mewmix/asm2464-enclosure/simulation/asm2464/upstream/emulate/hardware.py

"""
ASM2464PD Hardware Emulation

This module provides realistic hardware emulation for the ASM2464PD.
Only hardware registers (XDATA >= 0x6000) are emulated here.
RAM (XDATA < 0x6000) is handled by the memory system, not this module.
"""

from typing import TYPE_CHECKING, Dict, Set, Callable, Optional
from dataclasses import dataclass, field
from enum import IntEnum
import re
import os
import hashlib
import struct

from pyrite import PyriteDevice

if TYPE_CHECKING:
    from memory import Memory


# Physical SPI NOR geometry confirmed by two independent full-device dumps.
SPI_FLASH_SIZE = 0x80000
SPI_FLASH_ERASED_BYTE = 0xFF


def validate_stock_c24c_bridge_trace(events, config, link_param=0,
                                     initial_lane_mask=0,
                                     restore_b402=False):
    """Validate the ordered controller-visible core of stock C24C/CC83.

    ``events`` contains ``(bank, address, old, new)`` tuples.  Bank zero is
    normal MMIO and bank one is the DPX switch/PHY plane.  ``config`` is the
    four-byte SPI configuration slice at offsets 0x74..0x77, ordered exactly
    as stock 8C5F-8C86 loads it: vendor high/low, device high/low.

    This intentionally stops at C7A4's B436 lane configuration.  C24C's later
    3A2B call initializes stock-private queue tables. Its controller-visible
    history has a separate strict observer; the overlapping low-XDATA tables
    are not pretended to belong to the handmade firmware. Passing this
    validator therefore proves ordered bridge reconstruction only; it does
    not prove that silicon will generate C802.2/C520.1 after a 0206 descriptor.
    """
    if len(config) != 4:
        return False
    vendor_hi, vendor_lo, device_hi, device_lo = config

    # Each entry is bank, address, and either a direct value or an RMW mask.
    # RMW entries are (and_mask, or_value).  Keeping two writes to the same
    # register as two entries is deliberate: final-state equivalence is not
    # accepted for this undocumented bridge transaction.
    expected = [
        (0, 0xB401, (0xFE, 0x01)),
        (0, 0xB401, (0xFE, 0x00)),
        (0, 0xCA06, (0xEF, 0x00)),
        (0, 0xB410, vendor_lo), (0, 0xB411, vendor_hi),
        (0, 0xB420, vendor_lo), (0, 0xB421, vendor_hi),
        (0, 0xB412, device_lo), (0, 0xB413, device_hi),
        (0, 0xB422, device_lo), (0, 0xB423, device_hi),
        (0, 0xB415, 0x06), (0, 0xB416, 0x04), (0, 0xB417, 0x00),
        (0, 0xB425, 0x06), (0, 0xB426, 0x04), (0, 0xB427, 0x00),
        (0, 0xB41A, vendor_lo), (0, 0xB41B, vendor_hi),
        (0, 0xB42A, vendor_lo), (0, 0xB42B, vendor_hi),
        (0, 0xB418, device_lo), (0, 0xB419, device_hi),
        (0, 0xB428, device_lo), (0, 0xB429, device_hi),
        (1, 0x4084, 0x22), (1, 0x5084, 0x22),
        (0, 0xB401, (0xFE, 0x01)),
        (0, 0xB482, (0xFE, 0x01)),
        (0, 0xB482, (0x0F, 0xF0)),
        (0, 0xB401, (0xFE, 0x00)),
        (0, 0xB480, (0xFE, 0x01)),
        (0, 0xB430, (0xFE, 0x00)),
        (0, 0xB298, (0xEF, 0x10)),
        (1, 0x6043, 0x70), (1, 0x6025, (0x7F, 0x80)),
        (0, 0xCA06, (0xEF, 0x00)),
        (0, 0xB480, (0xFE, 0x01)),
        (0, 0xC659, (0xFE, 0x00)),
        (0, 0xB402, (0xFD, 0x00)),
    ]
    # BEA0 retains B434's upper nibble and progressively ORs masks 1,2,4,8
    # until all requested lanes are enabled. It can therefore perform zero to
    # four writes depending on the state inherited from the link path.
    initial_lane = initial_lane_mask & 0x0F
    lane = initial_lane
    for bit in (0x01, 0x02, 0x04, 0x08):
        if lane == 0x0F:
            break
        lane |= bit
        expected.append((0, 0xB434, (0xF0, lane)))
    if restore_b402:
        expected.append((0, 0xB402, (0xFD, 0x02)))
    expected.extend((
        (0, 0xB436, (0xF0, 0x0E)),
        (0, 0xB436, (0x0F, ((~link_param) & 0x0F) << 4)),
    ))
    if len(events) != len(expected):
        return False
    register_state = {}
    for event, requirement in zip(events, expected):
        bank, address, old, new = event
        expected_bank, expected_address, operation = requirement
        if bank != expected_bank or address != expected_address:
            return False
        key = (bank, address)
        if key in register_state and old != register_state[key]:
            return False
        register_state[key] = new
        if isinstance(operation, tuple):
            and_mask, or_value = operation
            wanted = (old & and_mask) | or_value
        else:
            wanted = operation
        if new != wanted:
            return False
    b402_clear = events[39]
    if bool(b402_clear[2] & 0x02) != bool(restore_b402):
        return False
    lane_events = [event for event in events if event[0:2] == (0, 0xB434)]
    if lane_events and (lane_events[0][2] & 0x0F) != initial_lane:
        return False
    return True


def validate_stock_cc83_bridge_trace(events, config):
    """Validate stock CC83 without C24C's caller prefix or lane tail."""
    if len(config) != 4:
        return False
    vendor_hi, vendor_lo, device_hi, device_lo = config
    expected = [
        (0, 0xCA06, (0xEF, 0x00)),
        (0, 0xB410, vendor_lo), (0, 0xB411, vendor_hi),
        (0, 0xB420, vendor_lo), (0, 0xB421, vendor_hi),
        (0, 0xB412, device_lo), (0, 0xB413, device_hi),
        (0, 0xB422, device_lo), (0, 0xB423, device_hi),
        (0, 0xB415, 0x06), (0, 0xB416, 0x04), (0, 0xB417, 0x00),
        (0, 0xB425, 0x06), (0, 0xB426, 0x04), (0, 0xB427, 0x00),
        (0, 0xB41A, vendor_lo), (0, 0xB41B, vendor_hi),
        (0, 0xB42A, vendor_lo), (0, 0xB42B, vendor_hi),
        (0, 0xB418, device_lo), (0, 0xB419, device_hi),
        (0, 0xB428, device_lo), (0, 0xB429, device_hi),
        (1, 0x4084, 0x22), (1, 0x5084, 0x22),
        (0, 0xB401, (0xFE, 0x01)),
        (0, 0xB482, (0xFE, 0x01)),
        (0, 0xB482, (0x0F, 0xF0)),
        (0, 0xB401, (0xFE, 0x00)),
        (0, 0xB480, (0xFE, 0x01)),
        (0, 0xB430, (0xFE, 0x00)),
        (0, 0xB298, (0xEF, 0x10)),
        (1, 0x6043, 0x70), (1, 0x6025, (0x7F, 0x80)),
    ]
    if len(events) != len(expected):
        return False
    register_state = {}
    for event, requirement in zip(events, expected):
        bank, address, old, new = event
        expected_bank, expected_address, operation = requirement
        if (bank, address) != (expected_bank, expected_address):
            return False
        key = (bank, address)
        if key in register_state and old != register_state[key]:
            return False
        register_state[key] = new
        wanted = ((old & operation[0]) | operation[1]
                  if isinstance(operation, tuple) else operation)
        if new != wanted:
            return False
    return True

# =============================================================================
# Register Name Lookup
# =============================================================================
# Parse registers.h to build addr -> name lookup table

_REGISTER_NAMES: Dict[int, str] = {}

def _load_register_names():
    """Parse registers.h and build address-to-name lookup table."""
    global _REGISTER_NAMES
    if _REGISTER_NAMES:
        return  # Already loaded

    # Find registers.h relative to this file
    this_dir = os.path.dirname(os.path.abspath(__file__))
    registers_h = os.path.join(this_dir, '..', 'src', 'include', 'registers.h')

    if not os.path.exists(registers_h):
        return

    # Pattern: #define REG_NAME  XDATA_REG8(0xADDR) or similar
    pattern = re.compile(r'#define\s+(REG_\w+)\s+XDATA_REG\d+\((0x[0-9A-Fa-f]+)\)')

    with open(registers_h, 'r') as f:
        for line in f:
            match = pattern.search(line)
            if match:
                name = match.group(1)
                addr = int(match.group(2), 16)
                _REGISTER_NAMES[addr] = name

def get_register_name(addr: int) -> str:
    """Get register name for address, or empty string if unknown."""
    _load_register_names()
    return _REGISTER_NAMES.get(addr, "")


class USBState(IntEnum):
    """
    USB state machine states.

    Matches firmware I_USB_STATE (IDATA[0x6A]) and USB_STATE_* constants in globals.h.
    State transitions occur in ISR at 0x0E68 and main loop at 0x202A.
    """
    DISCONNECTED = 0  # USB_STATE_DISCONNECTED - No USB connection
    ATTACHED = 1      # USB_STATE_ATTACHED - Cable connected
    POWERED = 2       # USB_STATE_POWERED - Bus powered
    DEFAULT = 3       # USB_STATE_DEFAULT - Default address assigned
    ADDRESS = 4       # USB_STATE_ADDRESS - Device address assigned
    CONFIGURED = 5    # USB_STATE_CONFIGURED - Ready for vendor commands


@dataclass
class USBCommand:
    """USB command queued for firmware processing."""
    cmd: int           # Command type (0xE4=read, 0xE5=write, 0x8A=scsi)
    addr: int          # Target XDATA address
    data: bytes        # Data for write commands
    response: bytes = b''  # Response data for read commands


class USBController:
    """
    USB controller emulation using only MMIO registers.

    This class manages the USB state machine and vendor command injection
    without directly modifying RAM. All state transitions are driven by
    setting MMIO registers that cause the firmware to naturally progress
    through its USB state machine.

    The firmware's USB state machine:
    - I_USB_STATE (IDATA[0x6A]) contains current USB state (0-5)
    - State 5 = USB_STATE_CONFIGURED, ready for vendor commands
    - Firmware transitions states by reading MMIO and updating its own RAM

    Key MMIO registers for USB (see registers.h for full definitions):
    - REG_USB_STATUS (0x9000): Connection status (bit 7=connected, bit 0=active)
    - REG_USB_PERIPH_STATUS (0x9101): Interrupt flags (bit 5 triggers cmd handler)
    - REG_USB_CTRL_PHASE (0x9091): Control transfer phase (bit 0=setup, bit 1=data)
    - REG_USB_DMA_TRIGGER (0x9092): Trigger DMA for descriptor transfer
    - REG_USB_DMA_STATE (0xCE89): DMA state machine (bits control transitions)
    - REG_USB_SETUP_* (0x9E00-0x9E07): USB setup packet buffer
    - REG_USB_EP0_COMPLETE (0xE712): EP0 transfer complete status

    Key globals for USB (see globals.h):
    - G_CMD_SLOT_INDEX (0x05A3): Current command slot index
    - G_CMD_TABLE_BASE (0x05B1): Command table (10 x 34-byte entries)
    - G_USB_CMD_CONFIG (0x07EC): USB command configuration
    - G_DMA_XFER_STATUS (0x0AA0): DMA transfer status
    """

    def __init__(self, hw: 'HardwareState'):
        self.hw = hw
        self.state = USBState.DISCONNECTED
        self.pending_cmd: Optional[USBCommand] = None
        self.enumeration_complete = False
        self.vendor_cmd_active = False

        # Track state machine progress
        self.state_machine_reads = 0
        self.enumeration_step = 0

        # Pending descriptor request from GET_DESCRIPTOR
        self.pending_descriptor_request = None

    def connect(self, speed: int = 2):
        """
        Simulate USB cable connection via MMIO registers.

        This sets the initial MMIO state that triggers USB enumeration
        in the firmware. The firmware will progress through states 0→5.

        Args:
            speed: USB speed mode:
                0 = Full Speed (USB 1.x, 12 Mbps)
                1 = High Speed (USB 2.0, 480 Mbps)
                2 = SuperSpeed (USB 3.x, 5 Gbps)
                3 = SuperSpeed+ (USB 3.1+, 10+ Gbps)
        """
        self.state = USBState.ATTACHED
        self.enumeration_step = 1
        self.usb_speed = speed

        # USB connection status registers
        # NOTE: 0x9000 bit 0 must be SET to enter USB state machine at 0x0E6E
        # At ISR 0x0E68: if bit 0 SET, jump to USB handling at 0x0E6E
        self.hw.regs[0x9000] = 0x81  # Bit 7 (connected), bit 0 SET for USB handling
        self.hw.regs[0x90E0] = speed  # USB speed
        self.hw.regs[0x9100] = speed  # USB link active with speed
        self.hw.regs[0x9105] = 0xFF  # PHY active
        # USB state indicator (0x9118):
        # At ISR 0x0E71, value is used as index into table at 0x5AC9
        # If table[0x9118] >= 8, USB handling is skipped
        # table[0] = 0x08 (skip), table[1] = 0x00 (continue)
        # Set to 1 to enable USB enumeration handling
        self.hw.regs[0x9118] = 0x01  # USB enumeration state (1 = pending setup)

        # USB interrupt and state machine triggers:
        # At 0x0FEB: if 0x9101 bit 6 CLEAR, skip USB init path
        # At 0x0FF2: if 0x90E2 bit 0 CLEAR, skip USB init path
        # So both bit 6 of 0x9101 and bit 0 of 0x90E2 must be SET
        self.hw.regs[0xC802] = 0x05  # USB interrupt pending (bits 0 + 2)
        self.hw.regs[0x9101] = 0x61  # Bit 6 SET (USB init), bit 5 SET, bit 0 for USB active
        self.hw.regs[0x90E2] = 0x03  # Bit 0 SET (USB init trigger), bit 1 SET

        # USB restart trigger at 0xCC5D:
        # At 0x2163-0x216B: if bit 0 CLEAR and bit 1 SET, calls USB restart at 0x2176
        # This sets 0x0A5A=1 which enables the USB init path at 0x2185
        self.hw.regs[0xCC5D] = 0x02  # Bit 1 SET, bit 0 CLEAR - triggers USB restart

        # USB PHY control at 0x91C0:
        # Firmware clears this during init, but at 0x203B it checks bit 1.
        # When state 0x0A59 == 2, if 0x92C2 bit 6 is SET and 0x91C0 bit 1 is SET,
        # firmware calls 0x0322 which progresses the USB state machine.
        self.hw.regs[0x91C0] = 0x02  # Bit 1 SET - enables USB state machine progress

        # USB mode indicators for descriptor handling at 0xA7E5 and 0x87A1:
        # At 0xA7E4-0xA7E5: checks 0xCC91 bit 1 for USB3 mode
        # At 0xA7FD-0xA7FF: checks 0x09F9 bit 6 for USB3 speed
        # If both set, 0x0ACC gets value with bit 1 SET, enabling USB3 descriptor path
        # For USB 2.0: clear these bits so firmware takes USB2 path
        if speed >= 2:  # SuperSpeed or higher
            self.hw.regs[0xCC91] = 0x02  # Bit 1 SET - USB3 mode
            self.hw.regs[0x09F9] = 0x40  # Bit 6 SET - USB3 speed indicator
        else:  # High Speed or Full Speed (USB 2.0)
            self.hw.regs[0xCC91] = 0x00  # Bit 1 CLEAR - USB2 mode
            self.hw.regs[0x09F9] = 0x00  # Bit 6 CLEAR - USB2 speed indicator

        # PCIe enumeration state - simulate that PCIe link is already up
        # In real hardware, PCIe enumeration happens during boot before USB control
        # transfers. The firmware checks this state at 0x185C before taking the
        # descriptor DMA path (0x1865+). Without it, firmware takes alternate path.
        #
        # Flow: 0x3803 checks XDATA[0x053F] or XDATA[0x0553] != 0
        #       If true, sets XDATA[0x0AF7] = 1 at 0x3914-0x3919
        #       This enables the "good" path at 0x185C that uses descriptor DMA
        #
        # CRITICAL: 0xB480 bit 0 must be SET to prevent firmware at 0x20DA from
        # taking the path at 0x20F9 that clears XDATA[0x0AF7] to 0.
        # At 0x20DA: jnb acc.0, 0x20fe -> if bit 0 CLEAR, jump and clear 0x0AF7
        self.hw.regs[0xB480] = 0x03  # Bits 0,1 SET - PCIe link active state

        # Set these to simulate completed PCIe enumeration:
        if self.hw.memory:
            self.hw.memory.xdata[0x0AF7] = 0x01  # PCIe enumeration complete flag
            self.hw.memory.xdata[0x053F] = 0x01  # PCIe link state (port 0)
            # CRITICAL: Command table state at G_CMD_TABLE_BASE + index*0x22 must NOT be 4
            # At 0x35D4-0x35DF: Firmware calls 0x1551 which reads G_CMD_SLOT_INDEX (0x05A3),
            # then calculates G_CMD_TABLE_BASE[index] and if that value equals 4,
            # it calls 0x54BB which clears XDATA[0x0AF7] to 0.
            # Set slot 0 state to 3 (ready) instead of 4 (error/reset).
            self.hw.memory.xdata[0x05A3] = 0x00  # G_CMD_SLOT_INDEX = 0
            self.hw.memory.xdata[0x05B1] = 0x03  # G_CMD_TABLE_BASE[0] = 3 (ready)

        print(f"[{self.hw.cycles:8d}] [USB_CTRL] Connected - MMIO set for enumeration")

    def inject_bot_cbw(self, cdb: bytes, *, tag: int = 1, transfer_length: int = 0,
                       direction_in: bool = False, lun: int = 0,
                       signature: bytes = b'USBC', cbw_length: int = 31,
                       flags: Optional[int] = None,
                       cdb_length: Optional[int] = None):
        """Inject a BOT CBW using the controller's parsed 0x911B layout."""
        if not self.hw.usb_bulk_engine_active:
            raise RuntimeError("BOT endpoint engine is not active")
        if not self.hw.usb_cbw_armed:
            raise RuntimeError("BOT CBW parser is not armed")
        if len(signature) != 4:
            raise ValueError("BOT signature must contain exactly four bytes")
        if not 1 <= len(cdb) <= 16:
            raise ValueError("BOT CDB length must be between 1 and 16 bytes")
        if not 0 <= transfer_length <= 0xFFFFFFFF:
            raise ValueError("BOT transfer length is outside uint32 range")

        regs = self.hw.regs
        regs[0x9119] = (cbw_length >> 8) & 0xFF
        regs[0x911A] = cbw_length & 0xFF
        for i, value in enumerate(signature):
            regs[0x911B + i] = value
        for i in range(4):
            regs[0x911F + i] = (tag >> (8 * i)) & 0xFF
            regs[0x9123 + i] = (transfer_length >> (8 * i)) & 0xFF
        regs[0x9127] = flags if flags is not None else (0x80 if direction_in else 0x00)
        regs[0x9128] = lun & 0xFF
        regs[0x9129] = len(cdb) if cdb_length is None else cdb_length
        for i in range(16):
            regs[0x912A + i] = cdb[i] if i < len(cdb) else 0

        self.hw.usb_stock_cbw_dma_trace = []
        self.hw.usb_stock_cbw_dma_ready = False
        self.hw.usb_stock_cbw_tag_trace = []
        self.hw.usb_stock_cbw_tag_ready = False
        self.hw.usb_stock_bulk_in_arm_trace = []
        self.hw.usb_stock_bulk_in_arm_ready = False
        self.hw.usb_stock_bulk_in_event_ready = False
        self.hw.usb_stock_bot_alt0_service_trace = []
        self.hw.usb_cbw_armed = False
        regs[0xC802] = 0x01
        regs[0x9101] = 0x40
        self.hw._pending_usb_interrupt = True

    def complete_msc_in(self, endpoint: int = 0x81):
        """Signal completion of the last firmware-originated MSC IN transfer."""
        self.hw.regs[0x9118] = endpoint
        # Stock's BOT-alt-zero 0EF4 route requires 9096.0 in addition to
        # C802.0/9101.5. This is a modeled host-completion event, not endpoint
        # state synthesized from descriptors.
        self.hw.regs[0x9096] = self.hw.regs.get(0x9096, 0) | 0x01
        self.hw.usb_ep_ready_ack_pending = True
        self.hw.regs[0xC802] = 0x01
        self.hw.regs[0x9101] = 0x20
        self.hw._pending_usb_interrupt = True

    def inject_bot_data_out(self, data: bytes, *, buffer_offset: int = 0):
        """Deliver one BOT OUT completion into the hardware's XDATA buffer.

        This is one controller completion, not necessarily one complete BOT data
        phase.  Physical SuperSpeed hardware completed a 4096-byte host write
        after its first 1024-byte packet.  Tests that pass 4096 bytes here are
        deliberately exercising idealized state-machine logic, not the observed
        endpoint packetization.
        """
        if len(data) > 0x1000:
            raise ValueError("BOT data-out exceeds the 4 KiB hardware buffer")
        if not 0 <= buffer_offset <= 0x1000 - len(data):
            raise ValueError("BOT data-out buffer range exceeds the 4 KiB hardware buffer")
        if not self.hw.memory:
            raise RuntimeError("BOT data-out requires attached XDATA memory")
        if self.hw.usb_sw_dma_out_destination is not None:
            start = self.hw.usb_sw_dma_out_destination
            self.hw.usb_sw_dma_out_destination = None
            if buffer_offset:
                raise ValueError(
                    "buffer_offset cannot override firmware-selected SW DMA")
        else:
            start = 0x7000 + buffer_offset
        if start + len(data) > len(self.hw.memory.xdata):
            raise ValueError("BOT data-out DMA range exceeds XDATA")
        self.hw.memory.xdata[start:start + len(data)] = data
        self.hw.regs[0x910D] = (len(data) >> 8) & 0xFF
        self.hw.regs[0x910E] = len(data) & 0xFF
        self.hw.regs[0x9093] = 0x02
        self.hw.regs[0xC802] = 0x01
        self.hw.regs[0x9101] = 0x04
        self.hw._pending_usb_interrupt = True

    def advance_enumeration(self):
        """
        Advance USB enumeration state via MMIO.

        Called when firmware polls 0xCE89 to check enumeration progress.
        Each call advances the emulated enumeration sequence.
        """
        self.state_machine_reads += 1

        # Return value for 0xCE89 based on enumeration progress
        value = 0x00

        if self.state_machine_reads >= 3:
            value |= 0x01  # Bit 0 - exit wait loop at 0x348C
            self.enumeration_step = max(self.enumeration_step, 2)

        if self.state_machine_reads >= 5:
            value |= 0x02  # Bit 1 - successful enumeration path at 0x3493
            self.enumeration_step = max(self.enumeration_step, 3)

        if self.state_machine_reads >= 7:
            value |= 0x04  # Bit 2 - state 3→4→5 transitions
            self.enumeration_step = max(self.enumeration_step, 4)
            self.enumeration_complete = True
            self.state = USBState.CONFIGURED

        return value

    def inject_vendor_command(self, cmd_type: int, xdata_addr: int,
                               value: int = 0, size: int = 1):
        """
        Inject a USB vendor command via MMIO registers.

        This sets up the MMIO registers needed for the firmware to process
        a vendor command. The firmware reads these registers and handles
        the command through its normal code path.

        No direct RAM writes are performed - the firmware reads expected
        values through MMIO hooks that simulate hardware behavior.

        Args:
            cmd_type: 0xE4 (read) or 0xE5 (write)
            xdata_addr: Target XDATA address
            value: Value for write commands
            size: Size for read commands
        """
        # Build USB address format: (addr & 0x1FFFF) | 0x500000
        usb_addr = (xdata_addr & 0x1FFFF) | 0x500000

        # Build 6-byte CDB (Command Descriptor Block)
        cdb = bytes([
            cmd_type,
            size if cmd_type == 0xE4 else value,
            (usb_addr >> 16) & 0xFF,
            (usb_addr >> 8) & 0xFF,
            usb_addr & 0xFF,
            0x00
        ])

        print(f"[{self.hw.cycles:8d}] [USB_CTRL] === INJECT VENDOR COMMAND ===")
        print(f"[{self.hw.cycles:8d}] [USB_CTRL] cmd=0x{cmd_type:02X} addr=0x{xdata_addr:04X} "
              f"{'size' if cmd_type == 0xE4 else 'val'}=0x{cdb[1]:02X}")
        print(f"[{self.hw.cycles:8d}] [USB_CTRL] CDB: {cdb.hex()}")

        # =====================================================
        # MMIO REGISTER SETUP FOR VENDOR COMMAND
        # =====================================================

        # Write CDB to USB interface registers (0x910D-0x9112)
        # Firmware reads these at 0x31C0+ to get command data
        for i, b in enumerate(cdb):
            self.hw.regs[0x910D + i] = b

        # Also populate 0x911F-0x9122 (another CDB location read by 0x3186)
        for i, b in enumerate(cdb[:4]):
            self.hw.regs[0x911F + i] = b

        # USB endpoint buffers
        for i, b in enumerate(cdb):
            self.hw.usb_ep_data_buf[i] = b
            self.hw.usb_ep0_buf[i] = b
        self.hw.usb_ep0_len = len(cdb)

        # USB connection and interrupt status
        # NOTE: 0x9000 bit 0 must be CLEAR to reach the 0x5333 vendor handler path
        # At 0x0E68, JB 0xe0.0 jumps away if bit 0 is set
        self.hw.regs[0x9000] = 0x80  # Connected (bit 7), bit 0 CLEAR for vendor path
        self.hw.regs[0x9101] = 0x21  # Bit 5 triggers command handler path
        self.hw.regs[0xC802] = 0x05  # USB interrupt pending

        # USB endpoint status - signals data available
        self.hw.regs[0x9096] = 0x01  # EP0 has data
        self.hw.regs[0x90E2] = 0x01  # Endpoint status bit

        # USB command interface registers
        self.hw.regs[0xE4E0] = cdb[0]  # Command type (0xE4/0xE5)
        self.hw.regs[0xE091] = size    # Read size / write value

        # Original firmware E5 path reads these (0x17FD-0x188B)
        # 0xC47A: Value byte copied to IDATA[0x38] at 0x1801
        # 0xCEB0: Command type copied to IDATA[0x39] at 0x188B
        self.hw.regs[0xC47A] = value if cmd_type == 0xE5 else size
        self.hw.regs[0xCEB0] = 0x05 if cmd_type == 0xE5 else 0x04

        # Target address registers (read at 0x323A-0x3249)
        # CEB2 = high byte of XDATA address
        # CEB3 = low byte of XDATA address
        self.hw.regs[0xCEB2] = (xdata_addr >> 8) & 0xFF
        self.hw.regs[0xCEB3] = xdata_addr & 0xFF

        # Store E5 value separately so it survives firmware clearing 0xC47A
        if cmd_type == 0xE5:
            self.hw.usb_e5_pending_value = value

        # USB EP0 data registers (read by various helpers)
        self.hw.regs[0x9E00] = cdb[0]  # bmRequestType / cmd type
        self.hw.regs[0x9E01] = cdb[1]  # bRequest / size
        self.hw.regs[0x9E02] = cdb[4]  # wValue low / addr low
        self.hw.regs[0x9E03] = cdb[3]  # wValue high / addr mid
        self.hw.regs[0x9E04] = cdb[2]  # wIndex low / addr high
        self.hw.regs[0x9E05] = 0x00    # wIndex high
        self.hw.regs[0x9E06] = size    # wLength low
        self.hw.regs[0x9E07] = 0x00    # wLength high

        # PCIe/DMA status for command processing
        self.hw.regs[0xC47B] = 0x01  # Non-zero for checks
        self.hw.regs[0xC471] = 0x01  # Queue busy
        self.hw.regs[0xB432] = 0x07  # PCIe link status
        self.hw.regs[0xE765] = 0x02  # Ready flag

        # Store command state
        self.hw.usb_cmd_type = cmd_type
        self.hw.usb_cmd_size = size if cmd_type == 0xE4 else 0
        self.hw.usb_cmd_pending = True
        self.vendor_cmd_active = True

        # Reset E5 DMA tracking flag for new command
        self.hw._e5_dma_done = False

        # Reset state machine for fresh command processing
        self.hw.usb_ce89_read_count = 0

        print(f"[{self.hw.cycles:8d}] [USB_CTRL] MMIO registers configured")

        # =====================================================
        # USB Hardware DMA - populate RAM like real hardware
        # =====================================================
        # The USB controller populates these RAM locations via DMA
        # before triggering the interrupt. This is how real hardware works.
        if self.hw.memory:
            # USB state = 5 (configured) - set by USB enumeration
            self.hw.memory.idata[0x6A] = 5

            # USB config check at 0x35C0 - must be 0 for vendor path
            self.hw.memory.xdata[0x07EC] = 0x00

            # CDB area - USB hardware writes CDB to XDATA[0x0002+]
            # The SCSI handler at 0x32E4 reads CDB from this area
            for i, b in enumerate(cdb):
                self.hw.memory.xdata[0x0002 + i] = b

            # Vendor command flag at 0x4583 - bit 3 enables vendor dispatch
            # This overlaps with CDB area but has special meaning
            self.hw.memory.xdata[0x0003] = 0x08

            # Command type marker for table lookup at 0x35D8
            if cmd_type == 0xE4:
                self.hw.memory.xdata[0x05B1] = 0x04
            elif cmd_type == 0xE5:
                self.hw.memory.xdata[0x05B1] = 0x05

            # Command index = 0 for table lookup at 0x1551
            # 0x17B1 copies 0x05A5 to 0x05A3, so set both to 0
            self.hw.memory.xdata[0x05A3] = 0x00
            self.hw.memory.xdata[0x05A5] = 0x00

        return cdb

    def inject_scsi_write_command(self, lba: int, sectors: int, data: bytes):
        """
        Inject a 0x8A SCSI write command via MMIO registers.

        This sets up the MMIO registers and RAM needed for the firmware to process
        a SCSI write command. The firmware reads these registers and handles
        the command through its normal code path.

        Args:
            lba: Logical Block Address to write to
            sectors: Number of sectors to write (each sector is 512 bytes)
            data: Data to write (will be padded to sector boundary)
        """
        import struct

        # Build 16-byte CDB for SCSI write command
        # Format: struct.pack('>BBQIBB', 0x8A, 0, lba, sectors, 0, 0)
        cdb = struct.pack('>BBQIBB', 0x8A, 0x00, lba, sectors, 0x00, 0x00)

        print(f"[{self.hw.cycles:8d}] [USB_CTRL] === INJECT SCSI WRITE COMMAND ===")
        print(f"[{self.hw.cycles:8d}] [USB_CTRL] LBA={lba} sectors={sectors} data_len={len(data)}")
        print(f"[{self.hw.cycles:8d}] [USB_CTRL] CDB: {cdb.hex()}")

        # =====================================================
        # MMIO REGISTER SETUP FOR SCSI COMMAND
        # =====================================================

        # Write CDB to USB interface registers (0x910D-0x911C)
        for i, b in enumerate(cdb):
            self.hw.regs[0x910D + i] = b

        # USB endpoint buffers - write CDB
        for i, b in enumerate(cdb):
            self.hw.usb_ep_data_buf[i] = b
            self.hw.usb_ep0_buf[i] = b
        self.hw.usb_ep0_len = len(cdb)

        # USB connection and interrupt status
        self.hw.regs[0x9000] = 0x80  # Connected (bit 7), bit 0 CLEAR
        self.hw.regs[0x9101] = 0x21  # Bit 5 triggers command handler path
        self.hw.regs[0xC802] = 0x05  # USB interrupt pending

        # USB endpoint status
        self.hw.regs[0x9096] = 0x01  # EP0 has data
        self.hw.regs[0x90E2] = 0x01  # Endpoint status bit

        # Store command state
        self.hw.usb_cmd_type = 0x8A
        self.hw.usb_cmd_size = sectors * 512
        self.hw.usb_cmd_pending = True
        self.vendor_cmd_active = True

        # Reset state machine
        self.hw.usb_ce89_read_count = 0

        print(f"[{self.hw.cycles:8d}] [USB_CTRL] MMIO registers configured for SCSI write")

        # =====================================================
        # RAM SETUP - populate RAM like USB hardware DMA
        # =====================================================
        if self.hw.memory:
            # USB state = 5 (configured)
            self.hw.memory.idata[0x6A] = 5

            # CDB area - USB hardware writes CDB to XDATA
            for i, b in enumerate(cdb):
                self.hw.memory.xdata[0x0002 + i] = b

            # SCSI command flag
            self.hw.memory.xdata[0x0003] = 0x08

            # Command type marker - 0x8A maps to different handler
            self.hw.memory.xdata[0x05B1] = 0x8A

            # Pad data to sector boundary and write to USB data buffer at 0x8000
            padded_size = sectors * 512
            padded_data = data + b'\x00' * (padded_size - len(data))
            for i, b in enumerate(padded_data):
                if 0x8000 + i < 0x10000:  # Stay within XDATA bounds
                    self.hw.memory.xdata[0x8000 + i] = b

            # Store data length info
            self.hw.usb_data_len = len(padded_data)

            print(f"[{self.hw.cycles:8d}] [USB_CTRL] Wrote {len(padded_data)} bytes to USB buffer at 0x8000")

        return cdb

    def inject_scsi_vendor_command(self, opcode: int, cdb: bytes, data: bytes = b'',
                                    is_write: bool = False):
        """
        Inject a SCSI vendor command (E0-E8) via MMIO registers.

        This sets up the MMIO registers needed for the firmware to process
        vendor-specific SCSI commands used by patch.py for firmware updates.

        Vendor opcodes:
            0xE0 - Config Read (128 bytes)
            0xE1 - Config Write (128 bytes)
            0xE2 - Flash Read
            0xE3 - Firmware Write (to SPI flash)
            0xE4 - XDATA Read
            0xE5 - XDATA Write
            0xE6 - NVMe Admin passthrough
            0xE8 - Reset/Commit

        Args:
            opcode: SCSI vendor opcode (0xE0-0xE8)
            cdb: Complete CDB bytes (16 bytes max)
            data: Data for write commands (E1, E3, E5)
            is_write: True if this is a write command with data phase
        """
        cycles = self.hw.cycles
        print(f"[{cycles:8d}] [USB_CTRL] === INJECT SCSI VENDOR COMMAND ===")
        print(f"[{cycles:8d}] [USB_CTRL] Opcode=0x{opcode:02X} CDB={cdb.hex()}")
        if is_write and data:
            print(f"[{cycles:8d}] [USB_CTRL] Write data: {len(data)} bytes")

        # Pad CDB to 16 bytes
        cdb_padded = (cdb + bytes(16))[:16]

        # =====================================================
        # MMIO REGISTER SETUP FOR SCSI VENDOR COMMAND
        # =====================================================

        # Write CDB to USB interface registers (0x910D-0x911C)
        for i, b in enumerate(cdb_padded):
            self.hw.regs[0x910D + i] = b

        # Also write to alternate CDB locations firmware may check
        for i, b in enumerate(cdb_padded):
            self.hw.regs[0x911F + i] = b

        # USB endpoint buffers
        for i, b in enumerate(cdb_padded):
            self.hw.usb_ep_data_buf[i] = b
            self.hw.usb_ep0_buf[i] = b
        self.hw.usb_ep0_len = len(cdb_padded)

        # USB connection and interrupt status
        self.hw.regs[0x9000] = 0x81  # Connected, USB active
        self.hw.regs[0x9101] = 0x21  # Bit 5 triggers command handler
        self.hw.regs[0xC802] = 0x05  # USB interrupt pending
        self.hw.regs[0x9096] = 0x01  # EP0 has data
        self.hw.regs[0x90E2] = 0x01  # Endpoint status

        # Store command state
        self.hw.usb_cmd_type = opcode
        self.hw.usb_cmd_size = len(data) if is_write else 0
        self.hw.usb_cmd_pending = True
        self.vendor_cmd_active = True

        # Reset state machine
        self.hw.usb_ce89_read_count = 0

        # =====================================================
        # RAM SETUP - populate like USB hardware DMA
        # =====================================================
        if self.hw.memory:
            # USB state = 2 (state for SCSI bulk commands)
            # Value 2 triggers the SCSI handler path at 0x32EE
            self.hw.memory.idata[0x6A] = 2

            # CDB area - write to XDATA[0x0002+] where firmware reads it
            for i, b in enumerate(cdb_padded):
                self.hw.memory.xdata[0x0002 + i] = b

            # Vendor command flags
            self.hw.memory.xdata[0x0003] = 0x08  # Enable vendor dispatch

            # Set state for vendor command handling
            # 0x0B02 = state machine: 0=idle, 1=E2 read, 2=E3 write
            if opcode == 0xE2:
                self.hw.memory.xdata[0x0B02] = 1
            elif opcode == 0xE3:
                self.hw.memory.xdata[0x0B02] = 2
            else:
                self.hw.memory.xdata[0x0B02] = 0

            # Magic value for vendor commands
            self.hw.memory.xdata[0xEA90] = 0x5A

            # Write data to USB buffer at 0x8000 for write commands
            if is_write and data:
                for i, b in enumerate(data):
                    if 0x8000 + i < 0x10000:
                        self.hw.memory.xdata[0x8000 + i] = b
                self.hw.usb_data_len = len(data)
                print(f"[{cycles:8d}] [USB_CTRL] Wrote {len(data)} bytes to USB buffer at 0x8000")

        print(f"[{cycles:8d}] [USB_CTRL] MMIO configured for vendor opcode 0x{opcode:02X}")
        return cdb_padded

    def inject_control_transfer(self, bmRequestType: int, bRequest: int, wValue: int,
                                  wIndex: int, wLength: int, data: bytes = b''):
        """
        Inject a USB control transfer (setup packet) through MMIO registers.

        This sets up the firmware's control transfer path:
        - Setup packet at 0x9E00-0x9E07
        - USB interrupt triggers handler at 0x0E33
        - Firmware reads setup packet and processes request

        ALL USB requests (standard and vendor) are passed through to firmware.
        The firmware handles GET_DESCRIPTOR by reading from code ROM via the
        flash mirror region (XDATA 0xE400-0xE500 → Code ROM).

        Args:
            bmRequestType: Request type byte (direction, type, recipient)
            bRequest: Request code (e.g., 0x06 = GET_DESCRIPTOR)
            wValue: Value field (e.g., descriptor type/index)
            wIndex: Index field
            wLength: Data length
            data: Data for OUT transfers
        """
        cycles = self.hw.cycles
        if data and (bmRequestType & 0x80):
            raise ValueError("control IN transfer cannot include OUT data")
        if data and len(data) != wLength:
            raise ValueError("control OUT data length does not match wLength")
        self.hw.pending_control_out_data = bytes(data)
        self.hw.usb_ep0_out_data_active = False
        print(f"[{cycles:8d}] [USB_CTRL] === INJECT CONTROL TRANSFER ===")
        print(f"[{cycles:8d}] [USB_CTRL] bmRequestType=0x{bmRequestType:02X} bRequest=0x{bRequest:02X}")
        print(f"[{cycles:8d}] [USB_CTRL] wValue=0x{wValue:04X} wIndex=0x{wIndex:04X} wLength={wLength}")

        # Write setup packet to MMIO registers
        # The firmware at 0xA5EA-0xA604 reads from 0x9104-0x910B (setup packet buffer)
        # and copies to XDATA 0x0ACE-0x0AD5
        self.hw.regs[0x9104] = bmRequestType
        self.hw.regs[0x9105] = bRequest
        self.hw.regs[0x9106] = wValue & 0xFF
        self.hw.regs[0x9107] = (wValue >> 8) & 0xFF
        self.hw.regs[0x9108] = wIndex & 0xFF
        self.hw.regs[0x9109] = (wIndex >> 8) & 0xFF
        self.hw.regs[0x910A] = wLength & 0xFF
        self.hw.regs[0x910B] = (wLength >> 8) & 0xFF

        # Also write to 0x9E00-0x9E07 (alternate setup packet location)
        self.hw.regs[0x9E00] = bmRequestType
        self.hw.regs[0x9E01] = bRequest
        self.hw.regs[0x9E02] = wValue & 0xFF
        self.hw.regs[0x9E03] = (wValue >> 8) & 0xFF
        self.hw.regs[0x9E04] = wIndex & 0xFF
        self.hw.regs[0x9E05] = (wIndex >> 8) & 0xFF
        self.hw.regs[0x9E06] = wLength & 0xFF
        self.hw.regs[0x9E07] = (wLength >> 8) & 0xFF

        # Also populate usb_ep0_buf which is what _usb_ep0_buf_read returns
        self.hw.usb_ep0_buf[0] = bmRequestType
        self.hw.usb_ep0_buf[1] = bRequest
        self.hw.usb_ep0_buf[2] = wValue & 0xFF
        self.hw.usb_ep0_buf[3] = (wValue >> 8) & 0xFF
        self.hw.usb_ep0_buf[4] = wIndex & 0xFF
        self.hw.usb_ep0_buf[5] = (wIndex >> 8) & 0xFF
        self.hw.usb_ep0_buf[6] = wLength & 0xFF
        self.hw.usb_ep0_buf[7] = (wLength >> 8) & 0xFF

        # USB connection and interrupt status
        # Bit 7 = connected, Bit 0 = active (needed for USB handler path at 0x4864)
        # With bit 0 CLEAR, firmware loops at 0x48CD checking CE89 instead of processing
        self.hw.regs[0x9000] = 0x81  # Connected (bit 7), Active (bit 0)
        self.hw.regs[0xC802] = 0x01  # USB interrupt pending

        # USB speed indicator - needed by 0xA4CC which returns 0x9100 & 0x03
        # 0 = Full Speed, 1 = High Speed, 2 = SuperSpeed, 3 = SuperSpeed+
        # At 0xB400: if speed == 2, sets R7=0 for descriptor DMA
        # Use stored USB speed from connect() or default to HIGH speed (USB 2.0)
        speed = getattr(self, 'usb_speed', 1)  # Default to High Speed if not set
        self.hw.regs[0x9100] = speed

        # USB mode indicators for descriptor handling at 0xA7E4-0xA7FF and 0x87A1
        # These set bits in 0x0ACC that determine USB2 vs USB3 code paths
        if speed >= 2:  # SuperSpeed or higher
            self.hw.regs[0xCC91] = 0x02  # Bit 1 SET - USB3 mode
            self.hw.regs[0x09F9] = 0x40  # Bit 6 SET - USB3 speed indicator
        else:  # High Speed or Full Speed (USB 2.0)
            self.hw.regs[0xCC91] = 0x00  # Bit 1 CLEAR - USB2 mode
            self.hw.regs[0x09F9] = 0x00  # Bit 6 CLEAR - USB2 speed indicator

        # Mark control transfer as active for state machine timing
        # This affects the 0x92C2 read callback bit 6 timing
        self.hw.usb_control_transfer_active = True
        self.hw.usb_ep0_fifo.clear()
        self.hw.usb_92c2_read_count = 0  # Reset for ISR->main loop timing
        self.hw.usb_ce89_read_count = 0  # Reset DMA state machine for new transfer

        # Check if this is a standard request (bmRequestType bits 6:5 = 00)
        request_type = bmRequestType & 0x60
        if request_type == 0x00:
            # Standard USB request (GET_DESCRIPTOR, SET_ADDRESS, etc.)
            # ISR path for GET_DESCRIPTOR (traced from original firmware):
            #   0x0E5E: checks 0x9101 bit 5 → if CLEAR, jumps to 0x0F07
            #   0x0F0B: checks 0x9101 bit 3 → if SET, goes to ISR dispatch (wrong path!)
            #   0x0F4A: if bit 3 CLEAR, reaches here
            #   0x0F4E: checks 0x9101 bit 0 → if CLEAR, jumps to 0x0F91
            #   0x0F91-0x0F95: checks 0x9101 bit 1 → if SET, calls 0x033B (descriptor handler!)
            # So for GET_DESCRIPTOR: need bit 3=0, bit 0=0, bit 1=1 → 0x02
            if bRequest == 0x06:  # GET_DESCRIPTOR
                desc_type = (wValue >> 8) & 0xFF
                desc_index = wValue & 0xFF
                print(f"[{cycles:8d}] [USB_CTRL] GET_DESCRIPTOR: type=0x{desc_type:02X} index=0x{desc_index:02X} len={wLength}")
                # Store the pending descriptor request for later DMA handling
                self.pending_descriptor_request = {
                    'type': desc_type,
                    'index': desc_index,
                    'length': wLength
                }
                # For GET_DESCRIPTOR: bit 1 SET to trigger descriptor handler, bits 0,3 CLEAR
                self.hw.regs[0x9101] = 0x02
                print(f"[{cycles:8d}] [USB_CTRL] Standard request - setting 0x9101=0x02, 0x9301=0x40")
            else:
                # Every standard request here is an EP0 control event. Bit 0
                # would misroute the handmade ISR into its reset handler.
                self.hw.regs[0x9101] = 0x02
                print(f"[{cycles:8d}] [USB_CTRL] Standard request - setting 0x9101=0x02, 0x9301=0x40")
            # 0x9301: Bit 6 triggers interrupt dispatch and DMA
            # Use write() to trigger the callback which handles descriptor DMA
            self.hw.write(0x9301, 0x40)  # Triggers _usb_9301_ep0_arm_write callback for DMA
        elif request_type == 0x20:
            # Class requests must be executed by firmware. In particular, do
            # not fake GET_MAX_LUN or BOT reset-recovery in the emulator.
            self.hw.regs[0x9101] = 0x22
            print(f"[{cycles:8d}] [USB_CTRL] Class request 0x{bRequest:02X} - passing to firmware")
        else:
            # Vendor request
            # Path: 0x0E33 → 0x0E64 → 0x0EF4 → 0x5333 (when 0x9101 bit 5 SET)
            self.hw.regs[0x9101] = 0x22  # Bit 1 = EP0 control, bit 5 SET (vendor path)
            print(f"[{cycles:8d}] [USB_CTRL] Vendor request - setting 0x9101=0x22")

        self.hw.regs[0x91D1] = 0x08  # EP0 setup packet received (bit 3)
        self.hw.regs[0x9118] = 0x01  # Endpoint index (lookup table requires < 8 value)

        # EP0 handler prerequisites
        # NOTE: 0x92C2 bit 6 is handled by _usb_92c2_read callback:
        #   - First read: returns bit 6 CLEAR (for ISR to call 0xBDA4)
        #   - Subsequent reads: returns bit 6 SET (for main loop to call 0x0322)
        self.hw.regs[0x92F8] = 0x0C  # Bits 2-3 set

        # CRITICAL: Main loop at 0xCDE7 checks 0x9091 bits for two-phase USB handling:
        # Phase 1 - Bit 0: Setup packet handler at 0xA5A6
        #   - Parses the USB request, sets 0x07E1 = 5 for GET_DESCRIPTOR
        #   - Firmware loops writing 0x01, waiting for hardware to clear bit 0
        # Phase 2 - Bit 1: DMA response handler at 0xD088
        #   - Checks 0x07E1 == 5, triggers DMA if so
        # 0x9002 bit 1 must be CLEAR to reach the 0x9091 check at 0xCDF5
        self.hw.regs[0x9002] = 0x00  # Bit 1 CLEAR to allow 0x9091 check
        self.hw.regs[0x9091] = 0x01  # Bit 0 SET to trigger setup handler at 0xA5A6
        # Reset phase transition counters
        self.hw._usb_9091_setup_writes = 0
        self.hw._usb_9091_read_count = 0

        # CRITICAL: The main loop at 0xCDC6-0xCDD9 waits for state transition registers:
        # - Checks 0xE712 bit 0 or bit 1 to exit the polling loop
        # - If neither set, checks 0xCC11 bit 1
        # Without these bits, firmware never reaches USB dispatch at 0xCDE7
        self.hw.regs[0xE712] = 0x01  # Bit 0 SET to exit polling loop
        self.hw.regs[0xCC11] = 0x02  # Bit 1 SET as backup exit condition

        # Set command pending
        self.hw.usb_cmd_pending = True
        self.vendor_cmd_active = False

        # USB state = 5 (configured) - required for firmware to process control transfers
        # The firmware checks this state at various decision points in the USB handler
        if self.hw.memory:
            self.hw.memory.idata[0x6A] = 5
            # PCIe enumeration complete flag - needed for descriptor DMA path at 0x185C
            # Without this, firmware takes alternate path that doesn't use CEB2/CEB3
            self.hw.memory.xdata[0x0AF7] = 0x01
            self.hw.memory.xdata[0x053F] = 0x01
            # CRITICAL: Port state at 0x05B1 + port_index*0x22 must NOT be 4
            # At 0x35D4-0x35DF: Firmware checks this and clears 0x0AF7 if state == 4
            self.hw.memory.xdata[0x05A3] = 0x00  # Port index = 0
            self.hw.memory.xdata[0x05B1] = 0x03  # Port 0 state = 3 (link up, not 4)
            # USB speed mode at 0x0AD6 - used by 0xB3FC at 0xB465 to check descriptor mode
            # At 0xB467: if 0x0AD6 >= 3, firmware returns R7=0x03 (wrong value for DMA)
            # This value would normally be set by USB enumeration before control transfers
            # Use stored USB speed from connect()
            usb_speed = getattr(self, 'usb_speed', 1)  # Default to High Speed if not set
            self.hw.memory.xdata[0x0AD6] = usb_speed  # USB speed mode

        # PCIe link state - 0xB480 bit 0 must be SET to prevent firmware at 0x20DA from
        # clearing XDATA[0x0AF7] to 0
        self.hw.regs[0xB480] = 0x03  # Bits 0,1 SET - PCIe link active state

        # Set pending interrupt flag so hardware update triggers actual CPU interrupt
        self.hw._pending_usb_interrupt = True

        print(f"[{cycles:8d}] [USB_CTRL] Control transfer injected (interrupt pending)")


@dataclass
class HardwareState:
    """
    Hardware state for ASM2464PD emulation.

    Only emulates actual hardware registers (addresses >= 0x6000).
    RAM variables are handled by the memory system.
    """

    # Logging
    log_reads: bool = False
    log_writes: bool = False
    log_uart: bool = True
    log_pcie: bool = True  # Log PCIe DMA operations

    # Proxy mode - when True, disable all fake USB/interrupt injection
    # Real hardware handles everything, we just proxy MMIO
    proxy_mode: bool = False

    # VID/PID override - intercept firmware USB descriptor writes to patch VID/PID
    # Format: (vid, pid) or None for no override
    vidpid_override: tuple = None

    # Reference to memory system (set by Emulator during init)
    # Used for reading XDATA (e.g., USB descriptors)
    _memory: 'Memory' = None

    # Cycle counter for timing-based responses
    cycles: int = 0

    # Hardware state
    usb_connected: bool = False
    usb_connect_delay: int = 500000  # Cycles before USB plug-in event (after init)

    # Polling counters - track how many times an address is polled
    poll_counts: Dict[int, int] = field(default_factory=dict)

    # Register values - only for hardware registers >= 0x6000
    regs: Dict[int, int] = field(default_factory=dict)
    dpx_regs: Dict[int, int] = field(default_factory=dict)

    # Callbacks for specific addresses
    read_callbacks: Dict[int, Callable[['HardwareState', int], int]] = field(default_factory=dict)
    write_callbacks: Dict[int, Callable[['HardwareState', int, int], None]] = field(default_factory=dict)

    # USB command queue
    usb_cmd_queue: list = field(default_factory=list)
    usb_cmd_pending: bool = False
    # The controller exposes a 512-byte EP0 staging window at 0x9E00-0x9FFF.
    # Keeping only the first max-packet here silently discarded the tail of
    # development-profile NVMe identify and data responses.
    usb_ep0_buf: bytearray = field(default_factory=lambda: bytearray(0x200))
    usb_ep0_len: int = 0
    usb_data_buf: bytearray = field(default_factory=lambda: bytearray(4096))  # Data buffer
    usb_data_len: int = 0
    usb_ep_data_buf: bytearray = field(default_factory=lambda: bytearray(2048))  # EP data buffer (0xD800)
    usb_sw_dma_out_destination: Optional[int] = None

    # Memory reference for E4/E5 commands (set by create_hardware_hooks)
    memory: 'Memory' = None

    # UART output buffer for line-based output
    uart_buffer: str = ""

    # USB command injection timing
    usb_injected: bool = False

    # USB controller instance (created in __post_init__)
    usb_controller: 'USBController' = None

    # USB command state for MMIO hooks
    usb_cmd_type: int = 0  # Current command type (0xE4, 0xE5, etc.)
    usb_cmd_size: int = 0  # Size for E4 read commands
    usb_e5_pending_value: int = 0  # Pending E5 value to write (preserved until read)

    # USB endpoint selection tracking
    usb_ep_selected: int = 0  # Currently selected endpoint index (0-31)

    # USB command injection from command line (set by emulator CLI)
    usb_inject_cmd: tuple = None  # (cmd_type, addr, val_or_size)
    usb_inject_delay: int = 1000  # Cycles after USB connect to inject

    # USB state machine emulation
    # Tracks firmware USB state to know when to set register bits
    usb_state_machine_phase: int = 0  # 0=init, 1=waiting, 2=enumerating, 3=ready
    usb_ce89_read_count: int = 0  # Count reads of 0xCE89 for state transitions
    usb_92c2_read_count: int = 0  # Count reads of 0x92C2 for ISR->main loop transition
    usb_ce00_read_count: int = 0  # Count reads of 0xCE00 for DMA completion
    scsi_dma_log: list = field(default_factory=list)
    scsi_dma_stall: bool = False
    scsi_dma_source_offset: int = 0

    # USB EP0 FIFO buffer - reserved for potential future use
    # Note: USB descriptor data is sent via hardware DMA from ROM, not firmware FIFO writes
    usb_ep0_fifo: bytearray = field(default_factory=bytearray)

    # USB control transfer active flag - affects 0x92C2 callback timing for ISR->main loop
    usb_control_transfer_active: bool = False

    # USB descriptor state
    # NOTE: The emulator does NOT track descriptor requests or generate responses.
    # The firmware handles GET_DESCRIPTOR by reading from code ROM and DMAing
    # the response to the USB buffer. See "USB Descriptor Handling Philosophy" above.
    usb_ep0_response: bytearray = field(default_factory=bytearray)  # Response data for host
    usb_transfer_complete: bool = False  # Set when firmware signals transfer complete
    # Firmware-originated MSC transfers captured when it writes the C42C trigger.
    usb_msc_transfers: list = field(default_factory=list)
    # Physical BOT endpoint state.  Descriptor presence does not imply that
    # the controller parser or transfer path exists: firmware must activate
    # 90E3 and explicitly arm the next CBW.
    usb_bulk_engine_active: bool = False
    usb_cbw_armed: bool = False
    usb_ep_ready_ack_pending: bool = False
    usb_endpoint_generation: int = 0
    usb_msc_trigger_log: list = field(default_factory=list)
    usb_msc_doorbell_trace: list = field(default_factory=list)
    usb_msc_pending_transfer: dict = None
    usb_sw_bulk_in_log: list = field(default_factory=list)
    usb_sw_bulk_in_fault: bool = False
    usb_sw_bulk_in_setup: dict = None
    # Exact stock buffered-IN preparation (0206 software branch) followed by
    # the BOT 47D5 -> 3258 service transaction.
    usb_stock_buffered_in_trace: list = field(default_factory=list)
    usb_stock_buffered_in_pending: dict = None
    usb_stock_buffered_in_log: list = field(default_factory=list)
    # BOT-alt-zero 4D3E -> 3258 service, independent of 0206.
    usb_stock_bot_alt0_service_trace: list = field(default_factory=list)
    usb_stock_c42c_completion_ack_pending: bool = False
    # Select the inferred hardware source raised after a valid 0206 history.
    # Tests exercise both statically proven consumers and a missing-source
    # failure; this selector is not physical evidence of either producer.
    usb_stock_completion_event_source: str = "c42c"
    # Stock BDA4's controller-visible prerequisite is distinct from the later
    # 0206 descriptor.  Physical silicon retained 90E1 when this state was
    # missing, so the model must be able to represent both outcomes.
    usb_stock_msc_prerequisite_trace: list = field(default_factory=list)
    usb_stock_52ef_trace: list = field(default_factory=list)
    usb_stock_52ef_ready: bool = False
    usb_stock_52ef_df0b_latched: bool = False
    usb_stock_5372_trace: list = field(default_factory=list)
    usb_stock_5372_ready: bool = False
    usb_stock_5372_df0b_latched: bool = False
    usb_stock_e300_trace: list = field(default_factory=list)
    usb_stock_e300_ready: bool = False
    usb_stock_e300_df0b_latched: bool = False
    usb_stock_4c8d_route_trace: list = field(default_factory=list)
    usb_stock_4c8d_route_ready: bool = False
    usb_stock_4c8d_c8cf_latched: bool = False
    usb_stock_c8cf_trace: list = field(default_factory=list)
    usb_stock_c8cf_ready: bool = False
    usb_stock_c8cf_cold_latched: bool = False
    usb_stock_cold_trace: list = field(default_factory=list)
    usb_stock_8fcf_trace: list = field(default_factory=list)
    usb_stock_8fcf_ready: bool = False
    usb_stock_dc3a_trace: list = field(default_factory=list)
    usb_stock_cold_cc83_trace: list = field(default_factory=list)
    usb_stock_cf91_trace: list = field(default_factory=list)
    usb_stock_df0b_stage: int = 0
    usb_stock_eeb5_eeaf_ready: bool = False
    usb_stock_dc3a_ready: bool = False
    usb_stock_ee8a_ready: bool = False
    usb_stock_cc32_ready: bool = False
    usb_stock_link_ready_observed: bool = False
    usb_stock_cold_cc83_ready: bool = False
    usb_stock_cold_ready: bool = False
    usb_stock_c24c_trace: list = field(default_factory=list)
    usb_stock_c24c_validated_trace: list = field(default_factory=list)
    usb_stock_msc_dma_ready: bool = False
    usb_stock_c24c_ready: bool = False
    usb_stock_msc_initial_transition_ready: bool = False
    usb_stock_b1c5_terminal_trace: list = field(default_factory=list)
    usb_stock_b1c5_terminal_ready: bool = False
    usb_stock_3a2b_channel_trace: list = field(default_factory=list)
    usb_stock_3a2b_channel_ready: bool = False
    usb_stock_3a2b_dma_trace: list = field(default_factory=list)
    usb_stock_3a2b_dma_ready: bool = False
    usb_stock_3a2b_scsi_dma_trace: list = field(default_factory=list)
    usb_stock_3a2b_scsi_dma_ready: bool = False
    usb_stock_cbw_dma_trace: list = field(default_factory=list)
    usb_stock_cbw_dma_ready: bool = False
    usb_stock_cbw_tag_trace: list = field(default_factory=list)
    usb_stock_cbw_tag_ready: bool = False
    usb_stock_bulk_in_arm_trace: list = field(default_factory=list)
    usb_stock_bulk_in_arm_ready: bool = False
    usb_stock_bulk_in_event_ready: bool = False
    # Default campaigns model prompt silicon completion. Focused regressions
    # may withhold it to reproduce a late 9101.2/9093.3 event.
    usb_stock_bulk_in_event_auto: bool = True
    usb_stock_msc_generation: int = 0
    usb_nvme_bulk_in_log: list = field(default_factory=list)
    usb_nvme_bulk_in_trace: list = field(default_factory=list)
    usb_nvme_bulk_in_ordered_log: list = field(default_factory=list)
    usb_nvme_bulk_in_fault: bool = False
    pending_control_out_data: bytes = b""

    # Config descriptor capture - firmware writes config descriptor to 0x9E00 but then
    # corrupts it before DMA. Capture the valid descriptor when written.
    usb_captured_config_desc: bytearray = field(default_factory=bytearray)
    usb_capture_config_active: bool = False  # True when we're capturing config desc writes

    # Full USB3 config descriptor loaded from ROM with corrected wTotalLength.
    # ROM at 0x58CF has wTotalLength=44 (only alt_setting 0), but alt_setting 1
    # data continues immediately after. We load the full descriptor (121 bytes)
    # and fix wTotalLength so the host knows to request all of it.
    usb_ss_config_from_rom: bytes = field(default_factory=bytes)

    # USB2 High Speed config descriptor loaded from ROM.
    # ROM at 0x5948 has USB 2.0 config descriptor with 512-byte max packet sizes.
    # Used when connected at USB 2.0 High Speed (dummy_hcd limitation).
    usb_hs_config_from_rom: bytes = field(default_factory=bytes)

    def reset_stock_msc_generation(self):
        """Revoke inferred MSC readiness across a firmware reset generation."""
        self.usb_stock_msc_prerequisite_trace = []
        self.usb_stock_52ef_trace = []
        self.usb_stock_52ef_ready = False
        self.usb_stock_52ef_df0b_latched = False
        self.usb_stock_5372_trace = []
        self.usb_stock_5372_ready = False
        self.usb_stock_5372_df0b_latched = False
        self.usb_stock_e300_trace = []
        self.usb_stock_e300_ready = False
        self.usb_stock_e300_df0b_latched = False
        self.usb_stock_4c8d_route_trace = []
        self.usb_stock_4c8d_route_ready = False
        self.usb_stock_4c8d_c8cf_latched = False
        self.usb_stock_c8cf_trace = []
        self.usb_stock_c8cf_ready = False
        self.usb_stock_c8cf_cold_latched = False
        self.usb_stock_cold_trace = []
        self.usb_stock_8fcf_trace = []
        self.usb_stock_8fcf_ready = False
        self.usb_stock_dc3a_trace = []
        self.usb_stock_cold_cc83_trace = []
        self.usb_stock_cf91_trace = []
        self.usb_stock_df0b_stage = 0
        self.usb_stock_eeb5_eeaf_ready = False
        self.usb_stock_dc3a_ready = False
        self.usb_stock_ee8a_ready = False
        self.usb_stock_cc32_ready = False
        self.usb_stock_link_ready_observed = False
        self.usb_stock_cold_cc83_ready = False
        self.usb_stock_cold_ready = False
        self.usb_stock_c24c_trace = []
        self.usb_stock_c24c_validated_trace = []
        self.usb_stock_msc_dma_ready = False
        self.usb_stock_c24c_ready = False
        self.usb_stock_msc_initial_transition_ready = False
        self.usb_stock_b1c5_terminal_trace = []
        self.usb_stock_b1c5_terminal_ready = False
        self.usb_stock_3a2b_channel_trace = []
        self.usb_stock_3a2b_channel_ready = False
        self.usb_stock_3a2b_dma_trace = []
        self.usb_stock_3a2b_dma_ready = False
        self.usb_stock_3a2b_scsi_dma_trace = []
        self.usb_stock_3a2b_scsi_dma_ready = False
        self.usb_stock_cbw_dma_trace = []
        self.usb_stock_cbw_dma_ready = False
        self.usb_stock_cbw_tag_trace = []
        self.usb_stock_cbw_tag_ready = False
        self.usb_stock_bulk_in_arm_trace = []
        self.usb_stock_bulk_in_arm_ready = False
        self.usb_stock_bulk_in_event_ready = False
        self.usb_stock_buffered_in_trace = []
        self.usb_stock_buffered_in_pending = None
        self.usb_stock_bot_alt0_service_trace = []
        self.usb_stock_c42c_completion_ack_pending = False

    def record_usb_stock_b1c5_terminal(self, addr: int, old: int, value: int):
        """Track BC07's ordered 09FA=4, 0AE1={1,2} terminal commit."""
        event = (addr, old, value)
        if addr == 0x09FA and value == 0x04:
            self.usb_stock_b1c5_terminal_trace = [event]
            self.usb_stock_b1c5_terminal_ready = False
            return
        if not self.usb_stock_b1c5_terminal_trace:
            return
        self.usb_stock_b1c5_terminal_trace.append(event)
        self.usb_stock_b1c5_terminal_ready = bool(
            len(self.usb_stock_b1c5_terminal_trace) == 2 and
            addr == 0x0AE1 and value in (0x01, 0x02))
        if not self.usb_stock_b1c5_terminal_ready:
            self.usb_stock_b1c5_terminal_trace = []

    def _record_usb_stock_3a2b_channel(self, addr: int, old: int, value: int):
        """Track 3A2B's reset prefix and eight channel-select writes."""
        relevant = (0xC8D8, 0xC8D7, 0xC8D6, 0xC8D5)
        if addr not in relevant or self.usb_stock_3a2b_channel_ready:
            return
        event = (addr, old, value)
        if (not self.usb_stock_3a2b_channel_trace and
                addr == 0xC8D8 and value == (old & ~0x08)):
            self.usb_stock_3a2b_channel_trace = [event]
        elif self.usb_stock_3a2b_channel_trace:
            self.usb_stock_3a2b_channel_trace.append(event)
        else:
            return
        trace = self.usb_stock_3a2b_channel_trace
        if len(trace) > 16:
            self.usb_stock_3a2b_channel_trace = []
            return
        if len(trace) != 16:
            return
        expected_addresses = [
            0xC8D8, 0xC8D8, 0xC8D8, 0xC8D7,
            0xC8D6, 0xC8D6, 0xC8D6, 0xC8D5,
            0xC8D8, 0xC8D8, 0xC8D8, 0xC8D8,
            0xC8D6, 0xC8D6, 0xC8D6, 0xC8D6]
        prefix_clears = (
            (0, 0x08), (1, 0x04), (2, 0x01),
            (4, 0x08), (5, 0x04), (6, 0x01))
        selector_ops = (
            (8, 0x02, True), (9, 0x02, True),
            (10, 0x02, False), (11, 0x02, False),
            (12, 0x02, True), (13, 0x02, True),
            (14, 0x02, False), (15, 0x02, False))
        self.usb_stock_3a2b_channel_ready = bool(
            [event[0] for event in trace] == expected_addresses and
            trace[3][2] == 0 and trace[7][2] == 0 and
            # C8D6/D8 contain hardware-owned status bits which may change
            # between the firmware's read and write. Pin the targeted clear
            # and its position without requiring unrelated bits to retain the
            # emulator's pre-read stored value.
            all(not (trace[index][2] & bit)
                for index, bit in prefix_clears) and
            all(self._usb_msc_transition(trace[index],
                                         expected_addresses[index], bit, set_bit)
                for index, bit, set_bit in selector_ops))

    def _record_usb_stock_3a2b_dma(self, addr: int, old: int, value: int):
        """Validate all eight 4AA0 selector/C8B2-C8B8 transactions."""
        relevant = {
            0xC8D8, 0xC8D6, 0xC8B2, 0xC8B3, 0xC8B4, 0xC8B5,
            0xC8B6, 0xC8B7, 0xC8B8}
        if addr not in relevant or self.usb_stock_3a2b_dma_ready:
            return
        # The first channel selector follows the eight-write reset prefix.
        if not self.usb_stock_3a2b_dma_trace:
            if (len(self.usb_stock_3a2b_channel_trace) != 9 or
                    addr not in (0xC8D8, 0xC8D6)):
                return
        self.usb_stock_3a2b_dma_trace.append((addr, old, value))
        trace = self.usb_stock_3a2b_dma_trace
        if len(trace) > 96:
            self.usb_stock_3a2b_dma_trace = []
            return
        if len(trace) != 96:
            return

        params = (
            (0xC8D8, True,  0xA0, 0x00, 0x0F, 0xFF),
            (0xC8D8, True,  0xB0, 0x00, 0x01, 0xFF),
            (0xC8D8, False, 0xA0, 0x00, 0x0F, 0xFF),
            (0xC8D8, False, 0xB0, 0x00, 0x01, 0xFF),
            (0xC8D6, True,  0xB8, 0x00, 0x03, 0xFF),
            (0xC8D6, True,  0xBC, 0x00, 0x00, 0x7F),
            (0xC8D6, False, 0xB8, 0x00, 0x03, 0xFF),
            (0xC8D6, False, 0xBC, 0x00, 0x00, 0x7F))
        valid = True
        expected_addresses = [
            None, 0xC8B7, 0xC8B6, 0xC8B6, 0xC8B6, 0xC8B6,
            0xC8B2, 0xC8B3, 0xC8B4, 0xC8B5, 0xC8B8, 0xC8B6]
        for index, expected in enumerate(params):
            chunk = trace[index * 12:(index + 1) * 12]
            selector, selected, aux, aux1, count_hi, count_lo = expected
            addresses = [event[0] for event in chunk]
            expected_addresses[0] = selector
            valid &= addresses == expected_addresses
            valid &= self._usb_msc_transition(
                chunk[0], selector, 0x02, selected)
            valid &= self._usb_msc_transition(chunk[2], 0xC8B6, 0x04, True)
            valid &= self._usb_msc_transition(chunk[3], 0xC8B6, 0x01, False)
            valid &= self._usb_msc_transition(chunk[4], 0xC8B6, 0x02, False)
            valid &= self._usb_msc_transition(chunk[5], 0xC8B6, 0x80, True)
            valid &= [event[2] for event in chunk[1:2] + chunk[6:11]] == [
                0x00, aux, aux1, count_hi, count_lo, 0x01]
            valid &= self._usb_msc_transition(chunk[11], 0xC8B6, 0x80, False)
        self.usb_stock_3a2b_dma_ready = bool(valid)

    def _record_usb_stock_3a2b_scsi_dma(self, addr: int, old: int,
                                        value: int):
        """Validate 3A2B's ordered CE40-CE43 per-slot reset tail."""
        if addr not in (0xCE40, 0xCE41, 0xCE42, 0xCE43):
            return
        if self.usb_stock_3a2b_scsi_dma_ready:
            return
        if not self.usb_stock_3a2b_dma_ready:
            self.usb_stock_3a2b_scsi_dma_trace = []
            return
        event = (addr, old, value)
        expected_addr = 0xCE40 + len(self.usb_stock_3a2b_scsi_dma_trace)
        if addr == expected_addr and value == 0:
            self.usb_stock_3a2b_scsi_dma_trace.append(event)
        elif addr == 0xCE40 and value == 0:
            self.usb_stock_3a2b_scsi_dma_trace = [event]
        else:
            self.usb_stock_3a2b_scsi_dma_trace = []
        self.usb_stock_3a2b_scsi_dma_ready = bool(
            len(self.usb_stock_3a2b_scsi_dma_trace) == 4)

    # PCIe DMA state
    pcie_dma_pending: bool = False  # DMA operation in progress
    pcie_dma_source: int = 0  # Source address in PCIe space
    pcie_dma_size: int = 0  # Size of transfer
    pcie_dma_dest: int = 0x8000  # Destination in XDATA (USB data buffer)

    # Simulated PCIe memory (for E4 read responses)
    # This would contain the data that would be read from the NVMe device
    pcie_memory: Dict[int, int] = field(default_factory=dict)

    # Minimal NVMe admin model used by handmade firmware tests.
    nvme_bar0: int = 0x00D00000
    nvme_cc: int = 0
    nvme_csts: int = 0
    nvme_controller_generation: int = 0
    nvme_asq: int = 0x00200000
    nvme_acq: int = 0x00820000
    nvme_cq_tail: int = 0
    nvme_cq_phase: int = 1
    nvme_admin_history: list = field(default_factory=list)
    nvme_last_security_send: bytes = b""
    nvme_security_send_history: list = field(default_factory=list)
    nvme_identify_serial: bytes = b"S65DNXMW601706".ljust(20, b" ")
    nvme_namespace_blocks: int = 1000215216
    nvme_namespace_lba_shift: int = 9
    nvme_namespace_present: bool = True
    nvme_io_cq_tail: int = 0
    nvme_io_cq_phase: int = 1
    nvme_io_cq_created: bool = False
    nvme_io_sq_created: bool = False
    nvme_io_history: list = field(default_factory=list)
    nvme_io_data_length: int = 0
    nvme_namespace_data: Dict[int, bytes] = field(default_factory=dict)
    nvme_io_status_fault: int = 0
    nvme_io_bus_reset_on_submit: bool = False
    pyrite_device: PyriteDevice = field(default_factory=PyriteDevice)

    # PCIe LTSSM State Machine & Link Emulation
    pcie_device_present: bool = True
    pcie_ltssm_state: int = 0x00
    pcie_ltssm_step: int = 0
    pcie_ltssm_auto_advance: bool = True
    pcie_ltssm_forced: Optional[int] = None
    pcie_ltssm_history: list = field(default_factory=list)
    pcie_e764_history: list = field(default_factory=list)
    pcie_rxpll_reset_history: list = field(default_factory=list)
    pcie_rxpll_e716_history: list = field(default_factory=list)
    pcie_rxpll_e716_pulse_complete: bool = False
    pcie_rxpll_reset_asserted: bool = False
    pcie_rxpll_reset_poll_observed: bool = False
    pcie_rxpll_reset_complete: bool = False
    pcie_rxpll_training_complete: bool = False
    pcie_acdf_history: list = field(default_factory=list)
    pcie_acdf_order_complete: bool = False
    pcie_link_recovery_history: list = field(default_factory=list)
    pcie_link_recovery_required: bool = False
    pcie_link_recovery_complete: bool = False

    # PCIe Programmed-I/O (PIO) Contract & Fault Hooks
    pcie_pio_history: list = field(default_factory=list)
    pcie_allow_legacy_4dw: bool = False
    pcie_pio_fault_timeout: bool = False
    pcie_pio_cpl_timeout: bool = False
    pcie_pio_b296_error: bool = False
    pcie_pio_cpl_status: int = 0x00
    pcie_pio_cpl_fmt: int = 0x04
    pcie_pio_cpl_dw0: int = 0x00
    pcie_pio_cpl_dw1: int = 0x00
    pcie_pio_stale_data: bool = False

    # PCIe Bridge Configuration Space (Type 1 Bridge)
    pcie_bridge_primary_bus: int = 0
    pcie_bridge_secondary_bus: int = 0
    pcie_bridge_subordinate_bus: int = 0
    pcie_bridge_command: int = 0
    pcie_bridge_status: int = 0x0010
    pcie_bridge_sec_latency: int = 0
    pcie_bridge_raw_mem_base: int = 0
    pcie_bridge_raw_mem_limit: int = 0
    pcie_bridge_mem_base: int = 0
    pcie_bridge_mem_limit: int = 0
    pcie_bridge_configured: bool = False

    # PCIe Endpoint Configuration Space (Type 0 Endpoint on Secondary Bus)
    pcie_endpoint_present: bool = True
    pcie_endpoint_devfn: int = 0x00
    pcie_endpoint_vendor_id: int = 0x144D
    pcie_endpoint_device_id: int = 0xA809
    pcie_endpoint_command: int = 0
    pcie_endpoint_status: int = 0x0010
    pcie_endpoint_class_code: int = 0x010802
    pcie_endpoint_rev_id: int = 0x00
    pcie_endpoint_bar0: int = 0
    pcie_endpoint_bar0_size: int = 0x01000000
    pcie_endpoint_bar0_probed: bool = False
    pcie_endpoint_bar0_is_io: bool = False
    pcie_endpoint_bar0_is_prefetchable: bool = False
    pcie_endpoint_bar0_is_64bit: bool = False
    pcie_endpoint_bars: list = field(default_factory=lambda: [0]*5)
    pcie_endpoint_capptr: int = 0x40
    pcie_endpoint_cap_id: int = 0x10
    pcie_endpoint_next_cap: int = 0x00
    pcie_endpoint_devctl: int = 0
    pcie_cfg_history: list = field(default_factory=list)
    # Routing validity is independent of whether configuration is currently
    # present. Reset must not turn absent BAR/window state into an MMIO bypass.
    # Isolated legacy encoder fixtures may explicitly opt out of this model.
    pcie_routing_gate_enforced: bool = True

    # Stock NVMe Queue Engine State & Fault Hooks (Queue 0 at 0xA000 / 0xB800)
    stock_nvme_queue_enabled: bool = False
    stock_nvme_setup_progress: int = 0
    stock_nvme_sq_tail: int = 0
    stock_nvme_cq_head: int = 0
    stock_nvme_cq_tail: int = 0
    stock_nvme_cq_phase: int = 1
    stock_nvme_head_history: list = field(default_factory=list)
    stock_nvme_submission_history: list = field(default_factory=list)
    stock_nvme_b296_timeout: bool = False
    stock_nvme_b296_error: bool = False
    stock_nvme_cq_b296_timeout: bool = False
    stock_nvme_cq_b296_error: bool = False
    stock_nvme_completion_timeout: bool = False
    stock_nvme_queue_error: bool = False
    stock_nvme_force_stale_phase: bool = False
    stock_nvme_force_mismatched_cid: bool = False
    stock_nvme_force_sct: int = 0
    stock_nvme_force_sc: int = 0

    # Stock NVMe Queue-1 I/O Engine State & Fault Hooks (Queue 1 at 0xA000 / 0xB840)
    stock_nvme_io_sq_tail: int = 0
    stock_nvme_io_cq_head: int = 0
    stock_nvme_io_cq_tail: int = 0
    stock_nvme_io_cq_phase: int = 1
    stock_nvme_io_head_history: list = field(default_factory=list)
    stock_nvme_io_submission_history: list = field(default_factory=list)
    stock_b254_trigger_log: list = field(default_factory=list)
    conventional_nvme_io_doorbell_count: int = 0
    stock_nvme_io_b296_timeout: bool = False
    stock_nvme_io_b296_error: bool = False
    stock_nvme_io_cq_b296_timeout: bool = False
    stock_nvme_io_cq_b296_error: bool = False
    stock_nvme_io_completion_timeout: bool = False
    stock_nvme_io_queue_error: bool = False
    stock_nvme_io_force_stale_phase: bool = False
    stock_nvme_io_force_mismatched_cid: bool = False
    stock_nvme_io_force_sct: int = 0
    stock_nvme_io_force_sc: int = 0
    stock_nvme_io_bus_reset_on_submit: bool = False

    # ============================================
    # SPI Flash Emulation
    # The ASM2464PD has a SPI flash chip for firmware storage.
    # patch.py uses E2 (read) and E3 (write) commands to access flash.
    # Physical target size: 512 KiB (0x80000 bytes), erased state 0xFF.
    # ============================================
    spi_flash: bytearray = field(
        default_factory=lambda: bytearray([SPI_FLASH_ERASED_BYTE]) * SPI_FLASH_SIZE
    )
    spi_flash_addr: int = 0  # Current flash address (set by address registers)
    spi_flash_write_pending: bool = False  # Write operation in progress
    spi_flash_write_count: int = 0  # Bytes written in current operation
    spi_command_log: list = field(default_factory=list)
    spi_program_fault: bool = False  # Drop page programs for readback-failure tests

    # Execution tracing
    trace_enabled: bool = False  # Global trace enable
    trace_points: Dict[int, str] = field(default_factory=dict)  # PC addr -> label
    trace_callback: Callable = None  # Optional callback(hw, pc, label) for trace points

    # XDATA write tracing - tracks writes to specific RAM addresses
    xdata_trace_enabled: bool = False
    xdata_trace_addrs: Dict[int, str] = field(default_factory=dict)  # addr -> name
    xdata_write_log: list = field(default_factory=list)  # Log of traced writes

    def __post_init__(self):
        """Initialize hardware register defaults."""
        self._init_registers()
        self._setup_callbacks()
        # Create USB controller after self is initialized
        self.usb_controller = USBController(self)

    def _init_registers(self):
        """
        Set default values for hardware registers.
        Only addresses >= 0x6000 are hardware registers.
        """
        self.pcie_e764_history.clear()
        self.pcie_rxpll_reset_history.clear()
        self.pcie_rxpll_e716_history.clear()
        self.pcie_rxpll_e716_pulse_complete = False
        self.pcie_rxpll_reset_asserted = False
        self.pcie_rxpll_reset_poll_observed = False
        self.pcie_rxpll_reset_complete = False
        self.pcie_rxpll_training_complete = False
        self.pcie_acdf_history.clear()
        self.pcie_acdf_order_complete = False
        self.pcie_link_recovery_history.clear()
        self.pcie_link_recovery_required = False
        self.pcie_link_recovery_complete = False
        self.reset_pcie_configuration()

        # ============================================
        # USB Controller Registers (0x9xxx)
        # ============================================
        self.regs[0x9000] = 0x00  # USB status - bit 7 = connected
        self.regs[0x90E0] = 0x00  # USB speed
        self.regs[0x9100] = 0x00  # USB link status
        self.regs[0x9105] = 0x00  # USB PHY status
        self.regs[0x91C0] = 0x02  # USB PHY control
        self.regs[0x91D0] = 0x00  # USB PHY config

        # ============================================
        # Power Management Registers (0x92xx)
        # ============================================
        self.regs[0x92C0] = 0x81  # Power enable
        self.regs[0x92C1] = 0x03  # Clocks enabled
        self.regs[0x92C2] = 0x40  # Power state - bit 6 enables PD task path at 0xBF44
        self.regs[0x92C5] = 0x04  # PHY powered
        self.regs[0x92E0] = 0x02  # Power domain
        self.regs[0x92F7] = 0x40  # Power status
        self.regs[0x92FB] = 0x01  # Power sequence complete (checked at 0x9C42)

        # ============================================
        # PD Event Registers (0xE4xx)
        # ============================================
        # These control the debug output at 0xAE89/0xAF5E
        # Set initial PD event to trigger debug output
        self.regs[0xE40F] = 0x00  # PD event type - will be set during PD events
        self.regs[0xE410] = 0x00  # PD sub-event

        # ============================================
        # PCIe Registers (0xBxxx)
        # ============================================
        self.regs[0xB238] = 0x00  # PCIe trigger - not busy
        self.regs[0xB254] = 0x00  # PCIe trigger write
        self.regs[0xB296] = 0x00  # PCIe status - bit 2 set when DMA complete
        self.regs[0xB401] = 0x01  # PCIe tunnel enabled
        self.regs[0xB480] = 0x00  # PCIe link initially down (bit 0 = 0)
        self.regs[0xB450] = 0x00  # PCIe LTSSM initially Detect.Quiet (0x00)
        # This allows USB state machine to return R7=5 at 0x3FC6 instead of state=11

        # ============================================
        # UART Registers (0xC0xx)
        # ============================================
        self.regs[0xC000] = 0x00  # UART TX data
        self.regs[0xC001] = 0x00  # UART TX data (alt)
        self.regs[0xC009] = 0x60  # UART LSR - TX empty, ready

        # ============================================
        # NVMe Controller Registers (0xC4xx, 0xC5xx)
        # ============================================
        self.regs[0xC412] = 0x02  # NVMe ready
        self.regs[0xC471] = 0x00  # NVMe queue busy - bit 0 = queue busy
        self.regs[0xC47A] = 0x00  # NVMe command status
        self.regs[0xC520] = 0x80  # NVMe link ready

        # ============================================
        # PHY Registers (0xC6xx)
        # ============================================
        self.regs[0xC620] = 0x00  # PHY control
        self.regs[0xC655] = 0x08  # PHY config
        self.regs[0xC65A] = 0x09  # PHY config
        self.regs[0xC6B3] = 0x30  # PHY status - bits 4,5 set

        # ============================================
        # Interrupt/DMA/Flash Registers (0xC8xx)
        # ============================================
        self.regs[0xC800] = 0x00  # Interrupt status
        self.regs[0xC802] = 0x00  # Interrupt status 2
        self.regs[0xC806] = 0x00  # System interrupt status
        self.regs[0xC80A] = 0x00  # PCIe/NVMe interrupt - bit 6 triggers PD debug
        self.regs[0xC8A9] = 0x00  # Flash CSR - not busy
        self.regs[0xC8AA] = 0x00  # Flash command
        self.regs[0xC8AB] = 0x00  # Flash address high
        self.regs[0xC8AC] = 0x00  # Flash address mid
        self.regs[0xC8AD] = 0x00  # Flash address low
        self.regs[0xC8AE] = 0x00  # Flash data register
        self.regs[0xC8B8] = 0x00  # Flash/DMA status
        self.regs[0xC8D6] = 0x04  # DMA status - done

        # ============================================
        # USB Power Delivery (PD) Registers (0xCAxx)
        # ============================================
        self.regs[0xCA00] = 0x00  # PD control
        self.regs[0xCA06] = 0x00  # PD status
        self.regs[0xCA0A] = 0x00  # PD interrupt control
        self.regs[0xCA0D] = 0x00  # PD interrupt status 1 - bit 3 = interrupt pending
        self.regs[0xCA0E] = 0x00  # PD interrupt status 2 - bit 2 = interrupt pending
        self.regs[0xCA81] = 0x00  # PD extended status

        # ============================================
        # Timer/CPU Control Registers (0xCCxx, 0xCDxx)
        # ============================================
        self.regs[0xCC11] = 0x00  # Timer 0 CSR
        self.regs[0xCC17] = 0x00  # Timer 1 CSR
        self.regs[0xCC1D] = 0x00  # Timer 2 CSR
        self.regs[0xCC23] = 0x00  # Timer 3 CSR
        self.regs[0xCC33] = 0x04  # CPU exec status
        self.regs[0xCC37] = 0x00  # CPU control
        self.regs[0xCC3B] = 0x00  # CPU control 2
        self.regs[0xCC3D] = 0x00  # CPU control 3
        self.regs[0xCC3E] = 0x00  # CPU control 4
        self.regs[0xCC3F] = 0x00  # CPU control 5
        self.regs[0xCC81] = 0x00  # Timer/DMA control
        self.regs[0xCC82] = 0x00  # Timer/DMA address low
        self.regs[0xCC83] = 0x00  # Timer/DMA address high
        self.regs[0xCC89] = 0x00  # Timer/DMA status - bit 1 = complete
        self.regs[0xCD31] = 0x01  # PHY init status - bit 0 = ready

        # ============================================
        # SCSI/DMA Registers (0xCExx)
        # ============================================
        self.regs[0xCE5D] = 0xFF  # Debug enable mask - all levels enabled
        self.regs[0xCE89] = 0x01  # SCSI DMA status - bit 0 = ready

        # NOTE: 0x707x addresses are NOT hardware registers!
        # They are flash buffer RAM (0x7000-0x7FFF) loaded from flash config.
        # Flash buffer is handled as regular XDATA, not MMIO.

        # ============================================
        # Debug/Command Engine Registers (0xE4xx)
        # ============================================
        self.regs[0xE40F] = 0x00  # PD event type (for debug output)
        self.regs[0xE410] = 0x00  # PD sub-event (for debug output)
        self.regs[0xE41C] = 0x00  # Command engine status

        # ============================================
        # System Status Registers (0xE7xx)
        # ============================================
        self.regs[0xE710] = 0x00  # System status
        self.regs[0xE712] = 0x00  # USB EP0 transfer status (bits 0,1 = complete)
        self.regs[0xE717] = 0x00  # System status 2
        self.regs[0xE751] = 0x00  # System status 3
        self.regs[0xE764] = 0x00  # System status 4
        self.regs[0xE795] = 0x21  # Flash ready + USB state 3 flag (bit 5)
        self.regs[0xE7E3] = 0x80  # PHY link ready

        # ============================================
        # PHY Completion / Debug Registers (0xE3xx)
        # ============================================
        self.regs[0xE302] = 0x40  # PHY completion status - bit 6 = complete

    def _setup_callbacks(self):
        """Setup read/write callbacks for hardware with special behavior."""
        # UART TX - capture output
        self.write_callbacks[0xC000] = self._uart_tx
        self.write_callbacks[0xC001] = self._uart_tx

        # PCIe status - complete after trigger
        self.read_callbacks[0xB296] = self._pcie_status_read
        self.write_callbacks[0xB254] = self._pcie_trigger_write

        # The synthetic stock-style queue engine is unavailable until firmware
        # executes the exact observed 83-byte setup tail in order.
        for setup_addr in (
                0xB264, 0xB265, 0xB266, 0xB267,
                0xB26C, 0xB26D, 0xB26E, 0xB26F,
                0xB250, 0xB251, 0xCEF0, 0xCEEF, 0xC807, 0xB281):
            self.write_callbacks[setup_addr] = self._stock_nvme_setup_write

        # PCIe DMA trigger - E4/E5 command DMA
        self.write_callbacks[0xB296] = self._pcie_dma_trigger

        # PCIe LTSSM State (0xB450) and control callbacks
        self.read_callbacks[0xB450] = self._pcie_ltssm_read
        self.write_callbacks[0xB450] = self._pcie_ltssm_write
        self.write_callbacks[0xB480] = self._pcie_perst_write
        self.write_callbacks[0xB403] = self._pcie_acdf_write
        self.write_callbacks[0xCA06] = self._pcie_acdf_write
        self.write_callbacks[0xCA81] = self._pcie_acdf_write
        self.write_callbacks[0xC656] = self._pcie_power_3v3_write
        self.write_callbacks[0xC65B] = self._pcie_power_companion_write
        self.write_callbacks[0xC659] = self._pcie_lane_gate_write
        self.write_callbacks[0xCC37] = self._pcie_cc37_write
        self.write_callbacks[0xE716] = self._pcie_e716_write
        self.write_callbacks[0xE764] = self._pcie_e764_write

        # Flash command configuration and transaction trigger.
        self.read_callbacks[0xC8A9] = self._flash_csr_read
        self.write_callbacks[0xC8A9] = self._flash_csr_write
        self.write_callbacks[0xC8AA] = self._flash_cmd_write

        # DMA status
        self.read_callbacks[0xC8D6] = self._dma_status_read

        # Flash/DMA busy - auto-clear
        self.read_callbacks[0xC8B8] = self._busy_reg_read

        # System interrupt status - clear on read
        self.read_callbacks[0xC806] = self._int_status_read

        # Stock NVMe Queue Engine Callbacks (CEF2, CEF3, B294)
        self.write_callbacks[0xCEF2] = self._cef2_write
        self.write_callbacks[0xCEF3] = self._cef3_write
        self.write_callbacks[0xB294] = self._b294_write

        # Timer CSRs
        for addr in [0xCC11, 0xCC17, 0xCC1D, 0xCC23, 0xCC5D]:
            self.read_callbacks[addr] = self._timer_csr_read
            self.write_callbacks[addr] = self._timer_csr_write

        # Unconditional controller-visible BDA4/DF86 prerequisite.  These
        # addresses have no other emulator side effects; CD31 and the timer
        # CSRs feed the same recorder from their existing callbacks.
        for addr in (0xC6A8, 0x92C8, 0xCC16, 0xCC18, 0xCC19,
                     0x92C4, 0x9201, 0xCC22, 0xCC1C, 0xCC1E, 0xCC1F,
                     0xCC5C, 0xCC5E, 0xCC5F):
            self.write_callbacks[addr] = self._usb_stock_prerequisite_write

        # Timer/DMA status register (0xCC89) - set complete bit after polling
        self.read_callbacks[0xCC89] = self._timer_dma_status_read

        # PHY init status - also handles descriptor DMA trigger on write
        self.read_callbacks[0xCD31] = self._phy_status_read
        self.write_callbacks[0xCD31] = self._phy_cmd_write

        # Command engine status
        self.read_callbacks[0xE41C] = self._cmd_engine_read

        # PD interrupt status - set by USB PD events
        self.read_callbacks[0xCA0D] = self._pd_interrupt_read
        self.read_callbacks[0xCA0E] = self._pd_interrupt_read

        # USB state machine MMIO registers (see registers.h for definitions)
        # REG_USB_DMA_STATE (0xCE89): USB/DMA status - controls state transitions
        #   USB_DMA_STATE_READY (bit 0): Must be set to exit wait loop (0x348C)
        #   USB_DMA_STATE_CBW (bit 1): 1=CBW received, 0=bulk data (0x3493)
        #   USB_DMA_STATE_ERROR (bit 2): DMA error in copy loop (0x3546)
        self.read_callbacks[0xCE89] = self._usb_ce89_read
        # REG_USB_DMA_ERROR (0xCE86): USB status - bit 4 checked at 0x349D
        self.read_callbacks[0xCE86] = self._usb_ce86_read
        # REG_XFER_STATUS_CE6C (0xCE6C): USB controller ready - bit 7 must be set
        self.read_callbacks[0xCE6C] = self._usb_ce6c_read
        # REG_SCSI_DMA_CTRL (0xCE00): DMA control register - returns 0 after completion
        # Firmware writes 0x03 to start DMA at 0x3531-0x3533, polls at 0x3534-0x3538
        self.read_callbacks[0xCE00] = self._usb_ce00_read
        self.write_callbacks[0xCE00] = self._usb_ce00_write
        # REG_SCSI_DMA_XFER_CNT (0xCE55): DMA transfer byte count after CE88/CE89 handshake
        # Read at 0x34B9 and stored to G_USB_WORK_009F as loop limit
        self.read_callbacks[0xCE55] = self._usb_ce55_read
        # REG_BULK_DMA_HANDSHAKE (0xCE88): DMA trigger - write resets state
        # At 0x1806: firmware writes to CE88 before polling REG_USB_DMA_STATE
        self.write_callbacks[0xCE88] = self._usb_ce88_write

        # USB setup/EP0 staging window (0x9E00-0x9FFF). Hardware writes the
        # eight-byte setup packet at its start; firmware reuses the complete
        # 512-byte window for control responses.
        for addr in range(0x9E00, 0xA000):
            self.read_callbacks[addr] = self._usb_ep0_buf_read
            self.write_callbacks[addr] = self._usb_ep0_buf_write

        # USB EP0 CSR (0x9E10)
        self.read_callbacks[0x9E10] = self._usb_ep0_csr_read
        self.write_callbacks[0x9E10] = self._usb_ep0_csr_write

        # USB EP data buffer (0xD800-0xDFFF) - endpoint data for bulk/control transfers
        for addr in range(0xD800, 0xE000):
            self.read_callbacks[addr] = self._usb_ep_data_buf_read
            self.write_callbacks[addr] = self._usb_ep_data_buf_write
        self.write_callbacks[0x90E1] = self._usb_sw_dma_trigger_write
        for addr in (0x9006, 0x905A, 0xC509, 0xC8D4):
            self.write_callbacks[addr] = self._usb_stock_buffered_sequence_write
        for addr in (0x9007, 0x9008, 0x9093, 0x9094):
            self.write_callbacks[addr] = self._usb_stock_bulk_in_arm_write

        # USB endpoint selection/status registers
        self.read_callbacks[0xC4EC] = self._usb_ep_status_read
        self.write_callbacks[0xC4ED] = self._usb_ep_index_write
        self.read_callbacks[0xC4EE] = self._usb_ep_id_low_read
        self.read_callbacks[0xC4EF] = self._usb_ep_id_high_read

        # USB endpoint data ready registers (0x90A1-0x90C0)
        # These indicate which endpoints have data available
        for addr in range(0x90A1, 0x90C1):
            self.read_callbacks[addr] = self._usb_ep_data_ready_read
        self.write_callbacks[0x90A1] = self._usb_sw_bulk_in_trigger_write
        self.write_callbacks[0x90B0] = self._usb_nvme_sequence_write
        # Stock dispatch_0206 per-slot NVMe-to-USB triggers.
        for addr in range(0x9137, 0x9157):
            self.write_callbacks[addr] = self._usb_nvme_bulk_in_trigger_write
        self.write_callbacks[0x90E3] = self._usb_bulk_ep_command_write

        # USB endpoint status registers (0x9096-0x90A0)
        # These control whether command handler path is taken (0 = process cmd)
        for addr in range(0x9096, 0x90A1):
            self.read_callbacks[addr] = self._usb_ep_status_reg_read
        self.write_callbacks[0x9096] = self._usb_ep_ready_ack_write

        # USB EP buffer address registers (0x905B/0x905C)
        # Firmware writes DMA source address here, hardware DMAs from this address
        self.write_callbacks[0x905B] = self._usb_ep_buf_addr_write
        self.write_callbacks[0x905C] = self._usb_ep_buf_addr_write

        # USB E5 value register (0xC47A)
        # The firmware clears this register (writes 0xFF) before reading it.
        # We need to preserve the injected value until it's read by the E5 handler.
        self.read_callbacks[0xC47A] = self._usb_e5_value_read
        self.write_callbacks[0xC47A] = self._usb_e5_value_write

        # MSC bulk-IN trigger. This observes bytes produced by firmware; it does
        # not synthesize SCSI responses.
        self.write_callbacks[0x900B] = self._usb_msc_sequence_write
        self.write_callbacks[0x901A] = self._usb_msc_sequence_write
        self.write_callbacks[0xC42A] = self._usb_msc_sequence_write
        self.write_callbacks[0xC42C] = self._usb_msc_trigger_write
        self.write_callbacks[0xC42D] = self._usb_msc_sequence_write

        # USB EP0 transfer status (0xE712)
        # The firmware polls this waiting for bits 0 and 1 to be set
        # indicating EP0 control transfer complete
        self.read_callbacks[0xE712] = self._usb_ep0_transfer_status_read

        # USB PHY control (0x91C0)
        # Firmware clears this at 0xCA8C but needs bit 1 SET for USB state machine
        # at 0x203B to progress from state 2 (0x0A59=2).
        self.read_callbacks[0x91C0] = self._usb_91c0_read

        # USB power state (0x92C2)
        # ISR at 0xE42A needs bit 6 CLEAR to call descriptor init (0xBDA4)
        # Main loop at 0x202A needs bit 6 SET to call 0x0322 for transfer
        # After ISR completes (2+ reads), return bit 6 SET
        self.read_callbacks[0x92C2] = self._usb_92c2_read

        # NOTE: 0xC001 is UART TX only, not USB EP0 FIFO. Testing confirmed that
        # firmware outputs debug messages to 0xC001 even during control transfer
        # handling. USB descriptor data is sent via hardware DMA directly from the
        # descriptor table in ROM (around 0x0864), not through firmware byte copies.
        # The exact DMA mechanism needs further investigation.

        # USB EP0 DMA control (0x9092) - may trigger hardware DMA
        # The actual source address for descriptor DMA is likely set via other registers
        self.write_callbacks[0x9092] = self._usb_ep0_dma_trigger_write
        self.read_callbacks[0x9092] = self._usb_ep0_dma_status_read

        # USB control state register (0x9091)
        # Two-phase control transfer handling:
        #   Bit 0: Setup phase - triggers 0xA5A6 (setup packet handler)
        #   Bit 1: Data phase - triggers 0xD088 (DMA for descriptor response)
        # Firmware loops writing 0x01 waiting for hardware to clear bit 0
        self.read_callbacks[0x9091] = self._usb_9091_read
        self.write_callbacks[0x9091] = self._usb_9091_write

        # USB endpoint status (0x9301)
        # Bit 6 triggers interrupt dispatch to device descriptor handler
        # Hardware clears bit 6 after read (acknowledge behavior)
        # Write of 0x40 (bit 6) arms EP0 for descriptor transfer
        self.read_callbacks[0x9301] = self._usb_9301_status_read
        self.write_callbacks[0x9301] = self._usb_9301_ep0_arm_write

        # Flash/Code ROM mirror region (0xE400-0xE700)
        # This XDATA region mirrors code ROM with offset 0xDDFC
        # Used for reading USB descriptors stored in code ROM
        # Examples:
        #   XDATA 0xE423 → Code ROM 0x0627 (device descriptor)
        #   XDATA 0xE437 → Code ROM 0x063B (language ID)
        #   XDATA 0xE6xx → Code ROM 0x08xx (additional descriptors)
        for addr in range(0xE400, 0xE700):
            self.read_callbacks[addr] = self._flash_rom_mirror_read

    # ============================================
    # Execution Tracing
    # ============================================
    def add_trace_point(self, pc: int, label: str):
        """
        Add a trace point at a specific PC address.

        When execution reaches this PC, the label will be logged.
        """
        self.trace_points[pc] = label

    def add_e4_trace_points(self):
        """
        Add trace points for E4 command processing.

        These cover the vendor handler and E4 read path.
        """
        self.trace_points.update({
            0x35B7: "VENDOR_HANDLER",
            0x35C0: "check_07EC",
            0x35C5: "call_17B1",
            0x35CB: "call_043F",
            0x35CF: "check_R7_after_043F",
            0x35D4: "call_1551",
            0x35DA: "E4_CHECK",
            0x35DF: "call_54BB",
            0x35E2: "setup_pcie_regs",
            0x35F9: "call_3C1E",
            0x35FC: "check_R7_after_3C1E",
            0x3601: "check_0AA0",
            0x360A: "setup_xfer",
            0x3649: "call_1741_cleanup",
            0x36E4: "vendor_exit",
            0x54BB: "E4_READ_HANDLER",
            0x3C1E: "pcie_transfer",
        })
        self.trace_enabled = True

    def check_trace(self, pc: int) -> str:
        """
        Check if PC matches a trace point and log if enabled.

        Returns the label if a trace point was hit, else None.
        """
        if not self.trace_enabled:
            return None

        if pc in self.trace_points:
            label = self.trace_points[pc]
            print(f"[{self.cycles:8d}] [TRACE] 0x{pc:04X}: {label}")

            # Call custom callback if registered
            if self.trace_callback:
                self.trace_callback(self, pc, label)

            return label
        return None

    # ============================================
    # XDATA Write Tracing
    # ============================================
    def add_xdata_trace(self, addr: int, name: str):
        """
        Add a trace point for XDATA writes.

        When firmware writes to this address, it will be logged.
        """
        self.xdata_trace_addrs[addr] = name

    def add_vendor_xdata_traces(self):
        """
        Add trace points for vendor command related XDATA addresses.

        These cover the key RAM locations used in E4/E5 command processing.
        Names match definitions in globals.h.
        """
        self.xdata_trace_addrs.update({
            0x0002: "G_IO_CMD_STATE",           # CDB[0]
            0x0003: "G_EP_STATUS_CTRL",         # Vendor flag
            0x0004: "G_WORK_0004",              # CDB[2]
            0x05A3: "G_CMD_SLOT_INDEX",         # Current command slot (0-9)
            0x05A5: "G_CMD_INDEX_SRC",          # Command index source
            0x05B1: "G_CMD_TABLE_BASE[0]",      # Command table entry 0
            0x05B2: "G_CMD_TABLE_BASE[0]+1",    # Command table entry 0, byte 1
            0x05B3: "G_CMD_TABLE_BASE[0]+2",    # Command table entry 0, byte 2
            0x05D3: "G_CMD_TABLE_BASE[1]",      # Command table entry 1
            0x07EC: "G_USB_CMD_CONFIG",         # USB command configuration
            0x0AA0: "G_DMA_XFER_STATUS",        # DMA transfer status
        })
        # Also trace command table range (10 entries x 34 bytes each)
        for i in range(10):
            base = 0x05B1 + i * 0x22  # G_CMD_TABLE_ENTRY_SIZE = 0x22
            if base not in self.xdata_trace_addrs:
                self.xdata_trace_addrs[base] = f"G_CMD_TABLE_BASE[{i}]"
        self.xdata_trace_enabled = True

    def trace_xdata_write(self, addr: int, value: int, pc: int = 0):
        """
        Log an XDATA write if tracing is enabled for this address.

        Called by memory system write hooks.
        """
        if not self.xdata_trace_enabled:
            return

        if addr in self.xdata_trace_addrs:
            name = self.xdata_trace_addrs[addr]
            entry = f"[{self.cycles:8d}] [PC=0x{pc:04X}] WRITE {name} (0x{addr:04X}) = 0x{value:02X}"
            self.xdata_write_log.append(entry)
            print(entry)
        elif 0x05B1 <= addr < 0x05B1 + 0x22 * 10:
            # Command table range
            idx = addr - 0x05B1
            entry_num = idx // 0x22
            offset = idx % 0x22
            entry = f"[{self.cycles:8d}] [PC=0x{pc:04X}] WRITE CMD_TABLE[{entry_num}]+{offset} (0x{addr:04X}) = 0x{value:02X}"
            self.xdata_write_log.append(entry)
            print(entry)

    def print_xdata_trace_log(self):
        """Print the accumulated XDATA write log."""
        print("\n=== XDATA WRITE LOG ===")
        for entry in self.xdata_write_log:
            print(entry)

    # ============================================
    # UART Callbacks
    # ============================================
    def _uart_tx(self, hw: 'HardwareState', addr: int, value: int):
        """Handle UART transmit with message buffering.

        NOTE: 0xC001 was previously thought to be shared with USB EP0 FIFO,
        but testing shows it's UART-only. The firmware outputs debug messages
        like "[InternalPD_StateInit]" to 0xC001 even during USB control transfer
        handling. The actual USB EP0 descriptor data is sent via hardware DMA
        directly from the descriptor table in ROM (around 0x0864), not through
        firmware-driven byte copying to 0xC001.
        """
        if self.log_uart:
            if value == 0x0A:  # Newline - print buffered line
                if self.uart_buffer:
                    print(f"[{self.cycles:8d}] [UART] {self.uart_buffer}")
                    self.uart_buffer = ""
            elif value == 0x0D:  # Carriage return - ignore
                pass
            elif 0x20 <= value < 0x7F:  # Printable ASCII
                self.uart_buffer += chr(value)
                # Flush on ']' to show complete [message] blocks
                if chr(value) == ']':
                    print(f"[{self.cycles:8d}] [UART] {self.uart_buffer}")
                    self.uart_buffer = ""
            # For very long lines, flush periodically
            if len(self.uart_buffer) > 200:
                print(f"[{self.cycles:8d}] [UART] {self.uart_buffer}")
                self.uart_buffer = ""
        else:
            try:
                if 0x20 <= value < 0x7F or value in (0x0A, 0x0D):
                    print(chr(value), end='', flush=True)
            except:
                pass

    # ============================================
    # PCIe Callbacks
    # ============================================
    def _pcie_status_read(self, hw: 'HardwareState', addr: int) -> int:
        """PCIe status read at 0xB296."""
        return self.regs.get(addr, 0x00)

    def _pcie_trigger_write(self, hw: 'HardwareState', addr: int, value: int):
        """Execute one programmed-I/O TLP or stock queue trigger."""
        self.regs[addr] = value
        self.stock_b254_trigger_log.append(value)
        if value in (0x01, 0x11):
            if not self.stock_nvme_queue_enabled:
                self.regs[0xB296] = self.regs.get(0xB296, 0) | 0x01
            elif value == 0x01:
                self._stock_nvme_sq_doorbell()
            else:
                self._stock_nvme_cq_doorbell()
            return

        if value in (0x02, 0x12):
            if not self.stock_nvme_queue_enabled:
                self.regs[0xB296] = self.regs.get(0xB296, 0) | 0x01
            elif value == 0x02:
                self._stock_nvme_io_sq_doorbell()
            else:
                self._stock_nvme_io_cq_doorbell()
            return

        fmt = self.regs.get(0xB210, 0)
        tlp_ctrl = self.regs.get(0xB213, 0)
        tlp_length = self.regs.get(0xB216, 0)
        byte_en = self.regs.get(0xB217, 0)
        b218 = self.regs.get(0xB218, 0)
        b219 = self.regs.get(0xB219, 0)
        target = ((b218 << 24) |
                  (b219 << 16) |
                  (self.regs.get(0xB21A, 0) << 8) |
                  self.regs.get(0xB21B, 0))

        record = {
            "fmt": fmt,
            "tlp_ctrl": tlp_ctrl,
            "tlp_length": tlp_length,
            "byte_en": byte_en,
            "target": target,
            "b218": b218,
            "b219": b219,
            "value": value,
        }
        self.pcie_pio_history.append(record)

        # Fault injection hooks
        if self.pcie_pio_fault_timeout:
            return

        if self.pcie_pio_b296_error:
            self.regs[0xB296] = 0x05  # bit 0 (ERROR) + bit 2 (ENGINE_DONE)
            self.regs[0xB22A] = 0x20
            return

        # Configuration Space Operations:
        # CfgRd0 (0x04), CfgWr0 (0x44), CfgRd1 (0x05), CfgWr1 (0x45)
        if fmt in (0x04, 0x05, 0x44, 0x45):
            valid_cfg = (tlp_ctrl == 1 and tlp_length == 0x20)
            if not valid_cfg:
                self.regs[0xB22A] = 0x20
                self.regs[0xB22B] = 0x00
                self.regs[0xB22C] = 0x00
                self.regs[0xB22D] = 0x00
                self.regs[0xB296] = 0x05  # ERROR + DONE
                return

            reg_dw = ((self.regs.get(0xB21A, 0) << 8) | self.regs.get(0xB21B, 0)) >> 2
            self.pcie_cfg_history.append({
                "fmt": fmt,
                "bus": b218,
                "devfn": b219,
                "reg_dw": reg_dw,
                "byte_en": byte_en,
            })

            # Type 0 (Bridge root port)
            if fmt in (0x04, 0x44):
                if b218 != self.pcie_bridge_primary_bus or b219 != 0:
                    self.regs[0xB22A] = 0x20  # UR
                    self.regs[0xB22B] = self.pcie_pio_cpl_fmt
                    self.regs[0xB22C] = 0x00
                    self.regs[0xB22D] = 0x00
                    self.regs[0xB284] = 1 if fmt == 0x04 else 0
                    self.regs[0xB296] = 0x04 if self.pcie_pio_cpl_timeout else 0x06
                    return

                if fmt == 0x04:  # CfgRd0
                    data = 0
                    if reg_dw == 0:
                        data = 0x2464174C
                    elif reg_dw == 1:
                        data = (self.pcie_bridge_status << 16) | (self.pcie_bridge_command & 0xFFFF)
                    elif reg_dw == 6:
                        data = (self.pcie_bridge_sec_latency << 24) | (self.pcie_bridge_subordinate_bus << 16) | (self.pcie_bridge_secondary_bus << 8) | self.pcie_bridge_primary_bus
                    elif reg_dw == 8:
                        data = (self.pcie_bridge_raw_mem_limit << 16) | (self.pcie_bridge_raw_mem_base & 0xFFFF)
                    self.regs[0xB220] = (data >> 24) & 0xFF
                    self.regs[0xB221] = (data >> 16) & 0xFF
                    self.regs[0xB222] = (data >> 8) & 0xFF
                    self.regs[0xB223] = data & 0xFF
                    self.regs[0xB22A] = self.pcie_pio_cpl_status
                    self.regs[0xB22B] = self.pcie_pio_cpl_fmt
                    self.regs[0xB22C] = self.pcie_pio_cpl_dw0
                    self.regs[0xB22D] = self.pcie_pio_cpl_dw1
                    self.regs[0xB284] = 1
                    self.regs[0xB296] = 0x04 if self.pcie_pio_cpl_timeout else 0x06
                    return
                else:  # CfgWr0
                    write_succeeded = (
                        self.pcie_pio_cpl_status == 0x00 and
                        not self.pcie_pio_cpl_timeout and
                        not self.pcie_pio_b296_error
                    )
                    if write_succeeded:
                        self.pcie_bridge_configured = True
                    val = ((self.regs.get(0xB220, 0) << 24) |
                           (self.regs.get(0xB221, 0) << 16) |
                           (self.regs.get(0xB222, 0) << 8) |
                           self.regs.get(0xB223, 0))
                    if write_succeeded:
                        if reg_dw == 1:
                            self.pcie_bridge_command = val & 0xFFFF
                        elif reg_dw == 6:
                            self.pcie_bridge_primary_bus = val & 0xFF
                            self.pcie_bridge_secondary_bus = (val >> 8) & 0xFF
                            self.pcie_bridge_subordinate_bus = (val >> 16) & 0xFF
                        elif reg_dw == 8:
                            self.pcie_bridge_raw_mem_base = val & 0xFFFF
                            self.pcie_bridge_raw_mem_limit = (val >> 16) & 0xFFFF
                            self.pcie_bridge_mem_base = (val & 0xFFF0) << 16
                            self.pcie_bridge_mem_limit = (((val >> 16) & 0xFFF0) << 16) | 0xFFFFF
                    self.regs[0xB22A] = self.pcie_pio_cpl_status
                    self.regs[0xB22B] = self.pcie_pio_cpl_fmt
                    self.regs[0xB22C] = self.pcie_pio_cpl_dw0
                    self.regs[0xB22D] = self.pcie_pio_cpl_dw1
                    self.regs[0xB284] = 0
                    self.regs[0xB296] = 0x04 if self.pcie_pio_cpl_timeout else 0x06
                    return

            # Type 1 (Endpoint on secondary bus)
            else:
                is_match = (
                    self.pcie_endpoint_present and
                    b218 == self.pcie_bridge_secondary_bus and
                    b219 == self.pcie_endpoint_devfn
                )
                if not is_match:
                    self.regs[0xB22A] = 0x20  # UR status
                    self.regs[0xB22B] = self.pcie_pio_cpl_fmt
                    self.regs[0xB22C] = 0x00
                    self.regs[0xB22D] = 0x00
                    self.regs[0xB284] = 1 if fmt == 0x05 else 0
                    self.regs[0xB296] = 0x04 if self.pcie_pio_cpl_timeout else 0x06
                    return

                if fmt == 0x05:  # CfgRd1
                    data = 0
                    if reg_dw == 0:
                        data = (self.pcie_endpoint_device_id << 16) | self.pcie_endpoint_vendor_id
                    elif reg_dw == 1:
                        data = (self.pcie_endpoint_status << 16) | (self.pcie_endpoint_command & 0xFFFF)
                    elif reg_dw == 2:
                        data = (self.pcie_endpoint_class_code << 8) | (self.pcie_endpoint_rev_id & 0xFF)
                    elif reg_dw == 4:  # BAR0
                        if self.pcie_endpoint_bar0_probed:
                            mask = (~(self.pcie_endpoint_bar0_size - 1)) & 0xFFFFFFFF
                            if self.pcie_endpoint_bar0_is_io:
                                mask |= 0x01
                            if self.pcie_endpoint_bar0_is_prefetchable:
                                mask |= 0x08
                            if self.pcie_endpoint_bar0_is_64bit:
                                mask |= 0x04
                            data = mask
                        else:
                            data = self.pcie_endpoint_bar0
                    elif 5 <= reg_dw <= 9:
                        data = self.pcie_endpoint_bars[reg_dw - 5]
                    elif reg_dw == 13:  # CapPtr (0x34)
                        data = self.pcie_endpoint_capptr & 0xFF
                    elif reg_dw == (self.pcie_endpoint_capptr >> 2):
                        data = ((self.pcie_endpoint_next_cap & 0xFF) << 8) | (self.pcie_endpoint_cap_id & 0xFF)
                    elif reg_dw == (self.pcie_endpoint_capptr >> 2) + 2:
                        data = self.pcie_endpoint_devctl
                    self.regs[0xB220] = (data >> 24) & 0xFF
                    self.regs[0xB221] = (data >> 16) & 0xFF
                    self.regs[0xB222] = (data >> 8) & 0xFF
                    self.regs[0xB223] = data & 0xFF
                    self.regs[0xB22A] = self.pcie_pio_cpl_status
                    self.regs[0xB22B] = self.pcie_pio_cpl_fmt
                    self.regs[0xB22C] = self.pcie_pio_cpl_dw0
                    self.regs[0xB22D] = self.pcie_pio_cpl_dw1
                    self.regs[0xB284] = 1
                    self.regs[0xB296] = 0x04 if self.pcie_pio_cpl_timeout else 0x06
                    return
                else:  # CfgWr1
                    val = ((self.regs.get(0xB220, 0) << 24) |
                           (self.regs.get(0xB221, 0) << 16) |
                           (self.regs.get(0xB222, 0) << 8) |
                           self.regs.get(0xB223, 0))
                    write_succeeded = (
                        self.pcie_pio_cpl_status == 0x00 and
                        not self.pcie_pio_cpl_timeout and
                        not self.pcie_pio_b296_error
                    )
                    if write_succeeded:
                        if reg_dw == 1:
                            self.pcie_endpoint_command = val & 0xFFFF
                        elif reg_dw == 4:
                            if val == 0xFFFFFFFF:
                                self.pcie_endpoint_bar0_probed = True
                            else:
                                self.pcie_endpoint_bar0 = val
                                self.pcie_endpoint_bar0_probed = False
                        elif 5 <= reg_dw <= 9:
                            self.pcie_endpoint_bars[reg_dw - 5] = val
                        elif reg_dw == (self.pcie_endpoint_capptr >> 2) + 2:
                            self.pcie_endpoint_devctl = val
                    self.regs[0xB22A] = self.pcie_pio_cpl_status
                    self.regs[0xB22B] = self.pcie_pio_cpl_fmt
                    self.regs[0xB22C] = self.pcie_pio_cpl_dw0
                    self.regs[0xB22D] = self.pcie_pio_cpl_dw1
                    self.regs[0xB284] = 0
                    self.regs[0xB296] = 0x04 if self.pcie_pio_cpl_timeout else 0x06
                    return

        # Contract enforcement:
        # Stock 3DW MRd (0x00) vs 3DW MWr (0x40).
        # Requires B213=1, B216=0x20, B217=0x0F, B218=0x00, B219=0xD0.
        valid_3dw = (
            tlp_ctrl == 1 and
            tlp_length == 0x20 and
            byte_en == 0x0F
        )

        if valid_3dw and (self.pcie_routing_gate_enforced or getattr(self, "pcie_bridge_configured", False)):
            bridge_mse = bool(self.pcie_bridge_command & 0x02)
            bridge_window_valid = (self.pcie_bridge_mem_base <= target <= self.pcie_bridge_mem_limit)
            endpoint_mse = bool(self.pcie_endpoint_command & 0x02)
            bar0_mask = (~(self.pcie_endpoint_bar0_size - 1)) & 0xFFFFFFFF
            bar0_match = (
                self.pcie_endpoint_bar0 != 0 and
                ((target & bar0_mask) == (self.pcie_endpoint_bar0 & bar0_mask))
            )
            if not (bridge_mse and bridge_window_valid and endpoint_mse and bar0_match):
                # Routing gate failed: return Unsupported Request (UR) completion
                self.regs[0xB22A] = 0x20  # UR status
                self.regs[0xB22B] = 0x04 if fmt == 0x00 else 0x00
                self.regs[0xB22C] = 0x00
                self.regs[0xB22D] = 0x00
                self.regs[0xB284] = 1 if fmt == 0x00 else 0
                if self.pcie_pio_cpl_timeout:
                    self.regs[0xB296] = 0x04
                else:
                    self.regs[0xB296] = 0x06
                return

        if fmt == 0x00 and valid_3dw:
            result = self._nvme_mmio_read32(target)
            if not self.pcie_pio_stale_data:
                self.regs[0xB220] = (result >> 24) & 0xFF
                self.regs[0xB221] = (result >> 16) & 0xFF
                self.regs[0xB222] = (result >> 8) & 0xFF
                self.regs[0xB223] = result & 0xFF
            self.regs[0xB22A] = self.pcie_pio_cpl_status
            self.regs[0xB22B] = self.pcie_pio_cpl_fmt
            self.regs[0xB22C] = self.pcie_pio_cpl_dw0
            self.regs[0xB22D] = self.pcie_pio_cpl_dw1
            self.regs[0xB284] = 1
            if self.pcie_pio_cpl_timeout:
                self.regs[0xB296] = 0x04  # ENGINE_DONE without VALID_CPL
            else:
                self.regs[0xB296] = 0x06  # bit 1 (VALID_CPL) + bit 2 (ENGINE_DONE)
        elif fmt == 0x40 and valid_3dw:
            data = ((self.regs.get(0xB220, 0) << 24) |
                    (self.regs.get(0xB221, 0) << 16) |
                    (self.regs.get(0xB222, 0) << 8) |
                    self.regs.get(0xB223, 0))
            self._nvme_mmio_write32(target, data)
            self.regs[0xB22A] = self.pcie_pio_cpl_status
            self.regs[0xB22B] = 0x00
            self.regs[0xB22C] = self.pcie_pio_cpl_dw0
            self.regs[0xB22D] = self.pcie_pio_cpl_dw1
            self.regs[0xB284] = 0
            self.regs[0xB296] = 0x04  # bit 2 (ENGINE_DONE)
        elif self.pcie_allow_legacy_4dw and fmt in (0x20, 0x60):
            # Legacy 4DW compatibility mode when explicitly allowed
            if fmt == 0x20:
                result = self._nvme_mmio_read32(target)
                self.regs[0xB220] = (result >> 24) & 0xFF
                self.regs[0xB221] = (result >> 16) & 0xFF
                self.regs[0xB222] = (result >> 8) & 0xFF
                self.regs[0xB223] = result & 0xFF
                self.regs[0xB22A], self.regs[0xB22B] = 0x00, 0x04
                self.regs[0xB22C], self.regs[0xB22D] = 0x00, 0x00
                self.regs[0xB284] = 1
                self.regs[0xB296] = 0x06
            else:
                data = ((self.regs.get(0xB220, 0) << 24) |
                        (self.regs.get(0xB221, 0) << 16) |
                        (self.regs.get(0xB222, 0) << 8) |
                        self.regs.get(0xB223, 0))
                self._nvme_mmio_write32(target, data)
                self.regs[0xB22A], self.regs[0xB22B] = 0x00, 0x00
                self.regs[0xB22C], self.regs[0xB22D] = 0x00, 0x00
                self.regs[0xB284] = 0
                self.regs[0xB296] = 0x04
        else:
            # Contract violation: malformed 4DW, wrong length, missing prerequisites
            self.regs[0xB22A] = 0x20  # UR status
            self.regs[0xB22B] = 0x00
            self.regs[0xB22C] = 0x00
            self.regs[0xB22D] = 0x00
            self.regs[0xB296] = 0x05  # bit 0 (ERROR) + bit 2 (ENGINE_DONE)

    def reset_pcie_configuration(self):
        """Reset all PCIe bridge and endpoint configuration state to power-on defaults."""
        self.pcie_bridge_primary_bus = 0
        self.pcie_bridge_secondary_bus = 0
        self.pcie_bridge_subordinate_bus = 0
        self.pcie_bridge_command = 0
        self.pcie_bridge_status = 0x0010
        self.pcie_bridge_sec_latency = 0
        self.pcie_bridge_raw_mem_base = 0
        self.pcie_bridge_raw_mem_limit = 0
        self.pcie_bridge_mem_base = 0
        self.pcie_bridge_mem_limit = 0
        self.pcie_bridge_configured = False

        self.pcie_endpoint_present = True
        self.pcie_endpoint_devfn = 0x00
        self.pcie_endpoint_command = 0
        self.pcie_endpoint_bar0 = 0
        self.pcie_endpoint_bar0_probed = False
        self.pcie_endpoint_bar0_size = 0x01000000
        self.pcie_endpoint_bar0_is_io = False
        self.pcie_endpoint_bar0_is_prefetchable = False
        self.pcie_endpoint_bar0_is_64bit = False
        self.pcie_endpoint_bars = [0] * 5
        self.pcie_endpoint_capptr = 0x40
        self.pcie_endpoint_cap_id = 0x10
        self.pcie_endpoint_next_cap = 0x00
        self.pcie_endpoint_devctl = 0
        self.pcie_cfg_history.clear()

    # ============================================
    # PCIe LTSSM Stage-Specific Model Callbacks
    # ============================================
    def check_detect_quiet_to_active(self) -> dict:
        """
        Prerequisites for LTSSM transition: Detect.Quiet (0x00) -> Detect.Active (0x01).

        Physical / Stock Derivation:
        - Downstream device physically present (receiver termination present).
        - 3.3V power rail enabled (0xC656 bit 5) [Stock: 0x52FF cold power rail].
        - Downstream lane/power gate enabled (0xC659 bit 0).
        - Downstream reset released (0xB480 bit 0 set). Stock C24C/CC83 sets
          this operational bit; the clear at 0x365F follows NVMe shutdown.
        """
        device_present = self.pcie_device_present
        p_3v3 = bool(self.regs.get(0xC656, 0) & 0x20)
        lane_gate = bool(self.regs.get(0xC659, 0) & 0x01)
        perst_deasserted = bool(self.regs.get(0xB480, 0) & 0x01)
        ready = bool(device_present and p_3v3 and lane_gate and perst_deasserted)
        return {
            "ready": ready,
            "device_present": device_present,
            "power_3v3": p_3v3,
            "lane_gate": lane_gate,
            "perst_deasserted": perst_deasserted,
        }

    def check_detect_active_to_polling(self) -> dict:
        """
        Prerequisites for LTSSM transition: Detect.Active (0x01) -> Polling (0x10).

        Physical / Stock Derivation:
        - Detect.Quiet -> Detect.Active prerequisites satisfied.
        - Stock's bank-1 ECC3 RXPLL reset asserted CC37.2, observed the
          E712/CC11 completion poll, and deasserted CC37.2.
        - Stock CB6D/E53A RXPLL transaction completed with the exact E764
          low-nibble history 8,8,8,A,B,9. A literal 1C is rejected.
        - Tunnel stability bit set (0xB403 bit 0) [Stock: B403 bridge stability].
        - Tunnel link state cleared (0xB430 == 0x00) [Stock: 0xCCBF].
        - ACDF/C7A4 selected the native Gen3-x2 B434 lane mask 0x0C.
        """
        stage1 = self.check_detect_quiet_to_active()
        e764_training = bool(
            self.pcie_rxpll_reset_complete and
            self.pcie_rxpll_training_complete and
            (self.regs.get(0xE764, 0) & 0x0F) == 0x09
        )
        tunnel_ctrl_b403 = bool(self.regs.get(0xB403, 0) & 0x01)
        tunnel_link_state_b430 = (self.regs.get(0xB430, 0) == 0x00)
        native_x2_lane_mask = (self.regs.get(0xB434, 0) & 0x0F) == 0x0C
        ready = bool(stage1["ready"] and e764_training and tunnel_ctrl_b403 and
                     tunnel_link_state_b430 and native_x2_lane_mask)
        return {
            "ready": ready,
            "stage1": stage1["ready"],
            "rxpll_reset_complete": self.pcie_rxpll_reset_complete,
            "e764_training": e764_training,
            "tunnel_ctrl_b403": tunnel_ctrl_b403,
            "tunnel_link_state_b430": tunnel_link_state_b430,
            "native_x2_lane_mask": native_x2_lane_mask,
        }

    def check_polling_to_l0(self) -> dict:
        """
        Prerequisites for LTSSM transition: Polling (0x10) -> L0 (0x78).
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
